baddy57/Eurocrack-Synth/PCB/Project_BIG MODULE_2021-10-10_22-04-19/6692469059dd4fbcb03a7d1d1fd7e01f.png

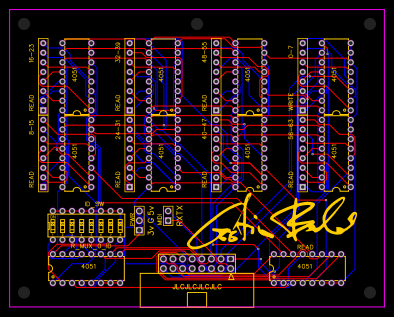
PCB/Project_BIG MODULE_2021-10-10_22-04-19/6692469059dd4fbcb03a7d1d1fd7e01f.png
