baddy57/Eurocrack-Synth/PCB/Project_BIG MODULE_2021-10-10_22-04-19/cb9d58b61e2843a09f57b589a00e0fff.png

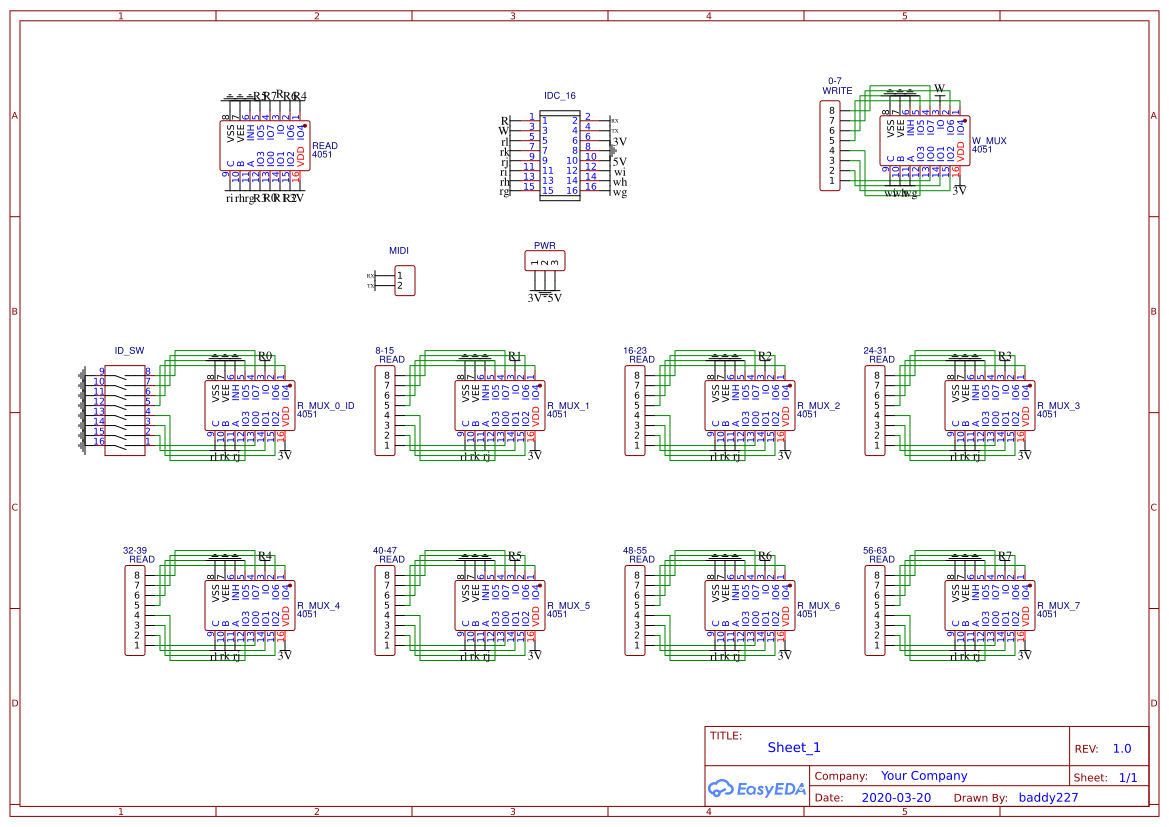
PCB/Project_BIG MODULE_2021-10-10_22-04-19/cb9d58b61e2843a09f57b589a00e0fff.png
