baddy57/Eurocrack-Synth/PCB/Project_MOBO_V3_2021-10-10_21-53-30/35c06b1600684f018b25b84a989f6b6b.png

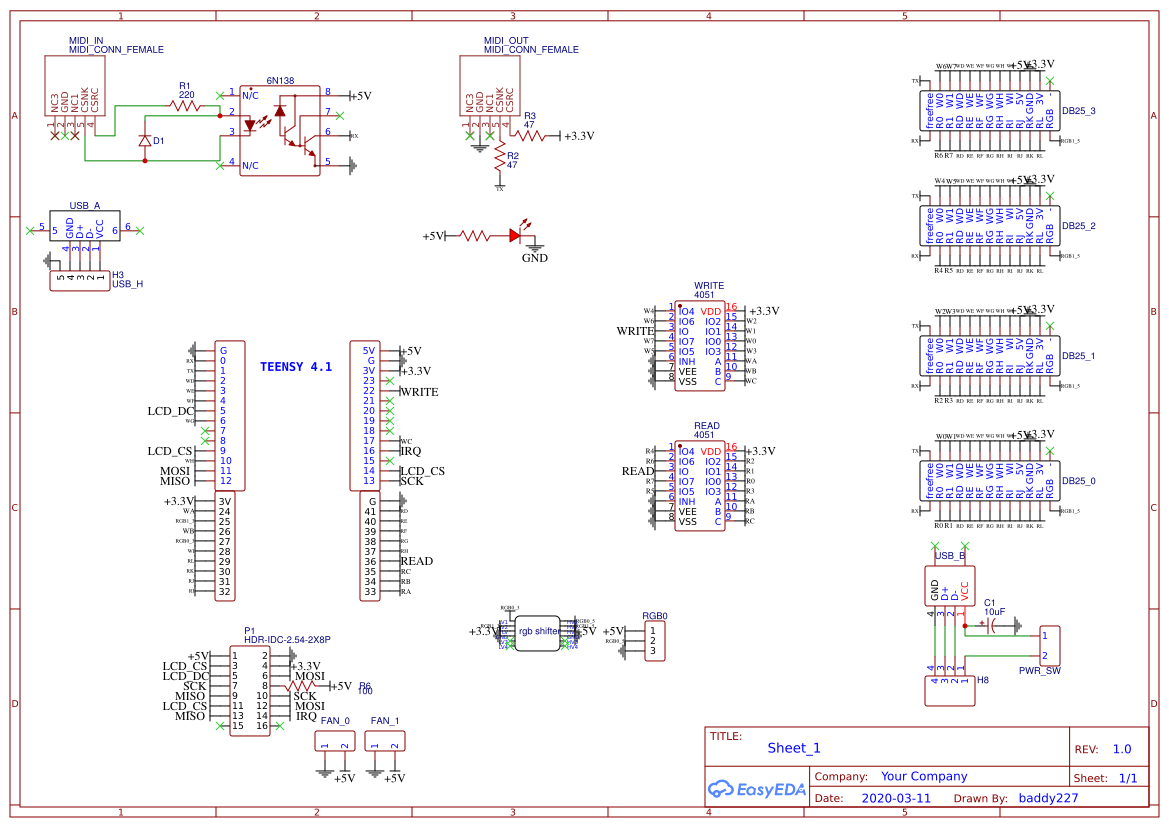
PCB/Project_MOBO_V3_2021-10-10_21-53-30/35c06b1600684f018b25b84a989f6b6b.png
