baddy57/Eurocrack-Synth/PCB/Project_MOBO_V3_2021-10-10_21-53-30/dce181980c11422688b88957aae91851.png

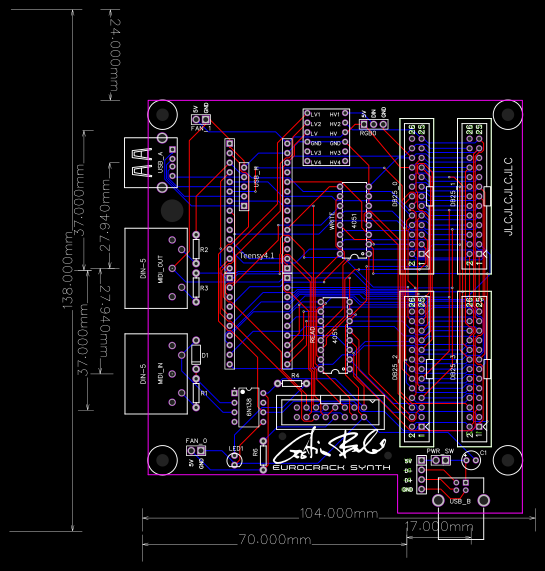
PCB/Project_MOBO_V3_2021-10-10_21-53-30/dce181980c11422688b88957aae91851.png
