baddy57/Eurocrack-Synth/PCB/Project_rack16_A_2021-10-10_22-05-13/7f478ecbd85349aaa525f855d9b86b6f.png

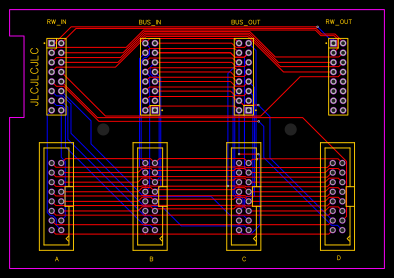
PCB/Project_rack16_A_2021-10-10_22-05-13/7f478ecbd85349aaa525f855d9b86b6f.png
