baddy57/Eurocrack-Synth/PCB/Project_rack16_A_2021-10-10_22-05-13/67f26889370e4767ae0cf2448eb2ead9.png

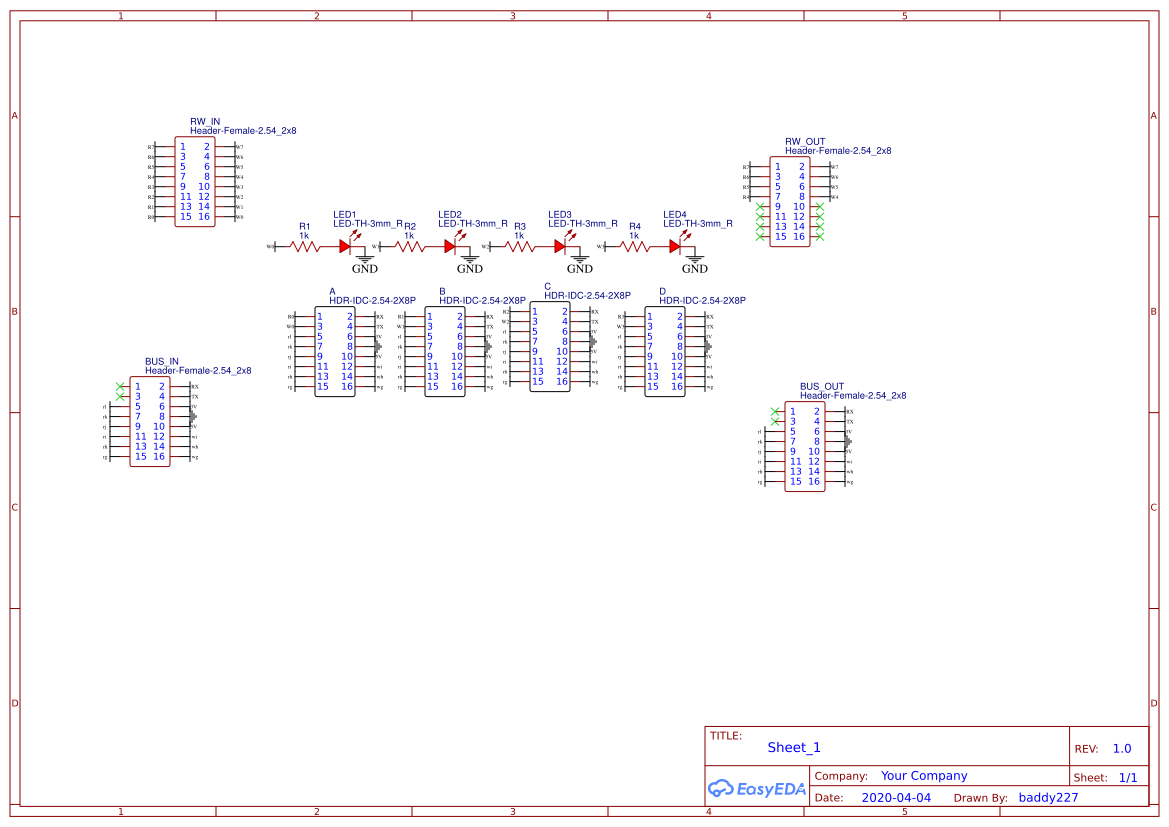
PCB/Project_rack16_A_2021-10-10_22-05-13/67f26889370e4767ae0cf2448eb2ead9.png
