baddy57/Eurocrack-Synth/PCB/Project_rack16_A_2021-10-10_22-05-13/b495c26256024feaad5c0fe8e8caf77f.png

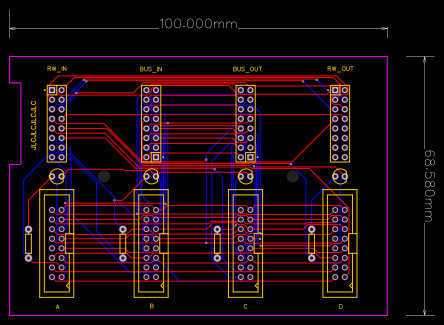
PCB/Project_rack16_A_2021-10-10_22-05-13/b495c26256024feaad5c0fe8e8caf77f.png
