baddy57/Eurocrack-Synth/PCB/Project_rack16_B_2021-10-10_22-06-08/38ca80ff898442d894452e9962c680d8.png

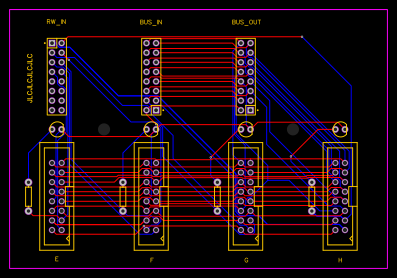
PCB/Project_rack16_B_2021-10-10_22-06-08/38ca80ff898442d894452e9962c680d8.png
