baddy57/Eurocrack-Synth/PCB/Project_RACK16_V3_2021-10-10_21-55-52/4ebbea798132460089381a975b632577.png

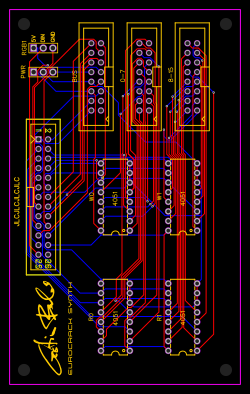
PCB/Project_RACK16_V3_2021-10-10_21-55-52/4ebbea798132460089381a975b632577.png
