baddy57/Eurocrack-Synth/PCB/Project_RACK16_V3_2021-10-10_21-55-52/cc3ec4de50fb47bfaea3014c30f05088.png

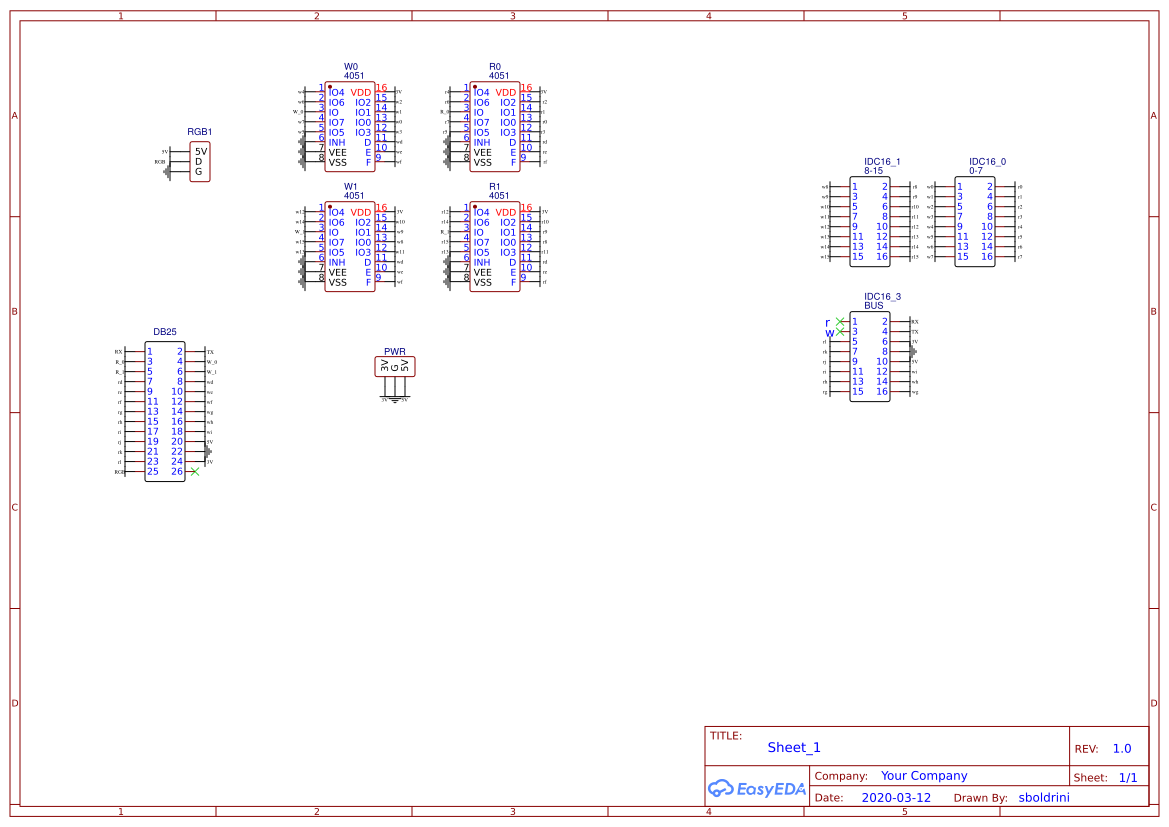
PCB/Project_RACK16_V3_2021-10-10_21-55-52/cc3ec4de50fb47bfaea3014c30f05088.png
