baddy57/Eurocrack-Synth/PCB/Project_SMALL MODULE_2021-10-10_22-03-08/b1a0076e745e476ea71988d6097ee347.png

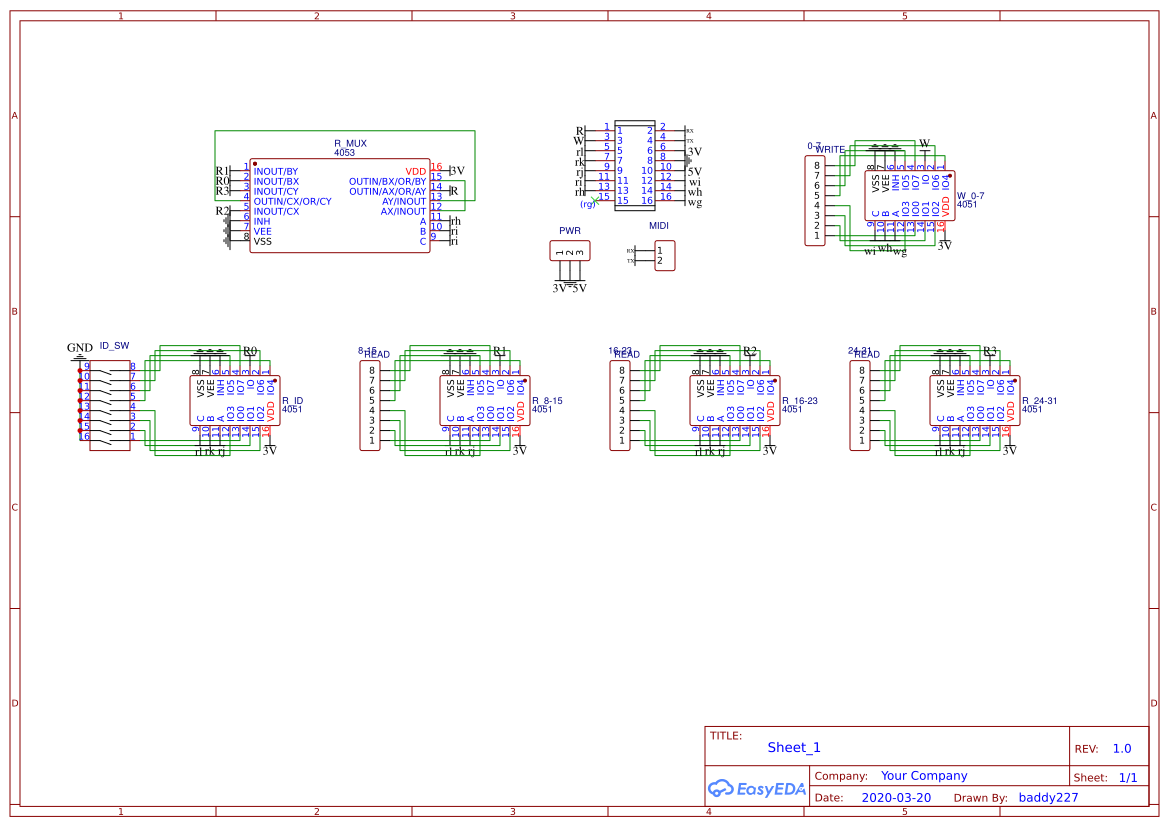
PCB/Project_SMALL MODULE_2021-10-10_22-03-08/b1a0076e745e476ea71988d6097ee347.png
