baddy57/Eurocrack-Synth/3D PARTS/MASTER BOX/ic_mic_48px-512.webp

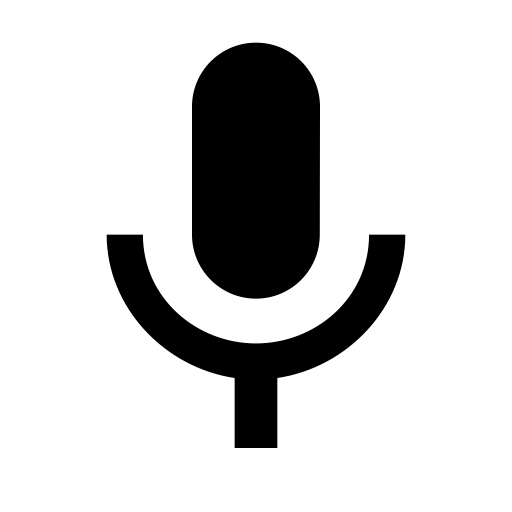
3D PARTS/MASTER BOX/ic_mic_48px-512.webp
