baddy57/Eurocrack-Synth/3D PARTS/MASTER BOX/PCB.png

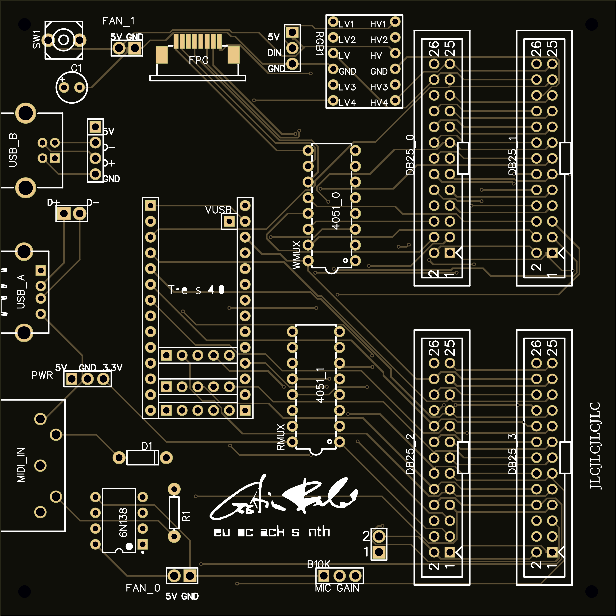
3D PARTS/MASTER BOX/PCB.png
