baddy57/Eurocrack-Synth/3D PARTS/MODULES/BIG PCB.jpg

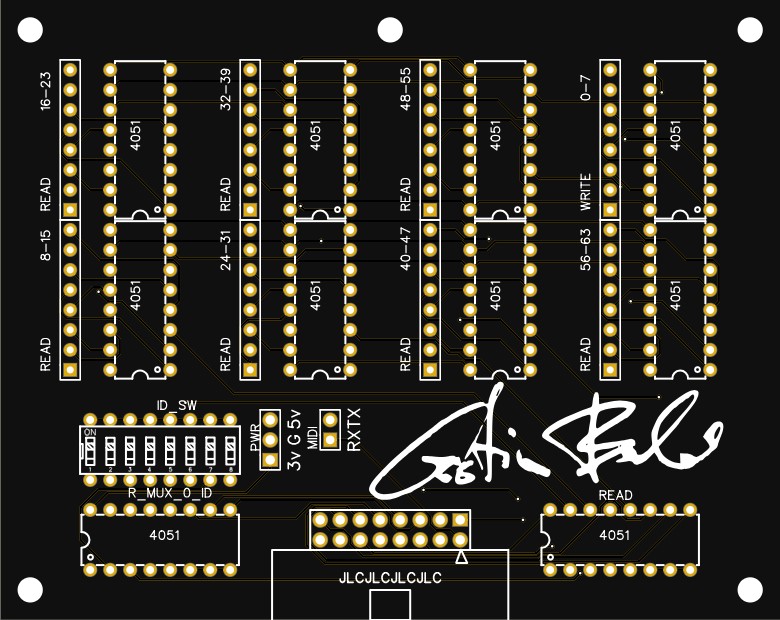
3D PARTS/MODULES/BIG PCB.jpg
