baddy57/Eurocrack-Synth/3D PARTS/MODULES/MODULE PCB TYPE A.png

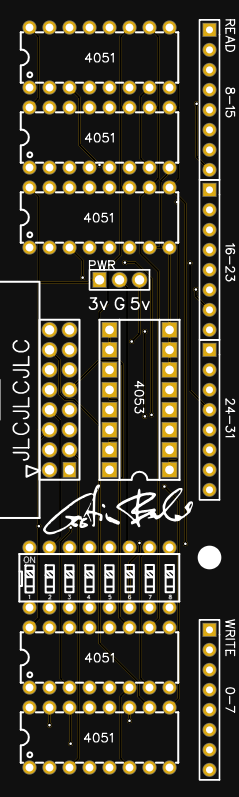
3D PARTS/MODULES/MODULE PCB TYPE A.png
