baddy57/Eurocrack-Synth/3D PARTS/RACK16/trash/Parametric_Eurorack_Rail2/images/62bd9fd48c2334298f00ef797886a475_preview_featured.jpg

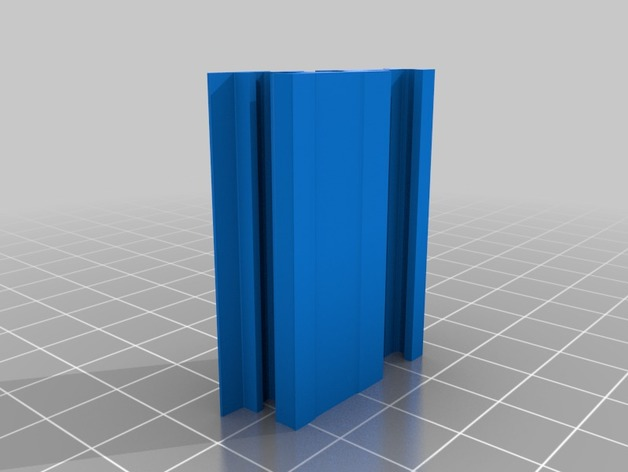
3D PARTS/RACK16/trash/Parametric_Eurorack_Rail2/images/62bd9fd48c2334298f00ef797886a475_preview_featured.jpg
