baddy57/Eurocrack-Synth/3D PARTS/RACK16/trash/Parametric_Eurorack_Rail/images/9bb14bf8cfc0c23107f52e55db40d1ac_preview_featured.JPG

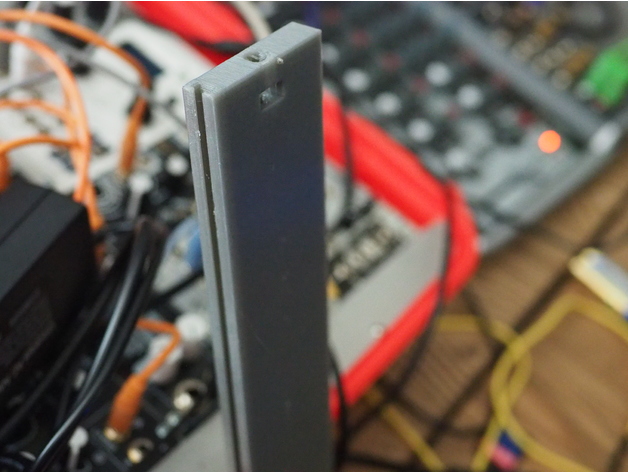
3D PARTS/RACK16/trash/Parametric_Eurorack_Rail/images/9bb14bf8cfc0c23107f52e55db40d1ac_preview_featured.JPG
