baddy57/Eurocrack-Synth/3D PARTS/RACK16/trash/Parametric_Eurorack_Rail/images/365d9e6f2081d008faea3ab9caef1937_preview_featured.jpg

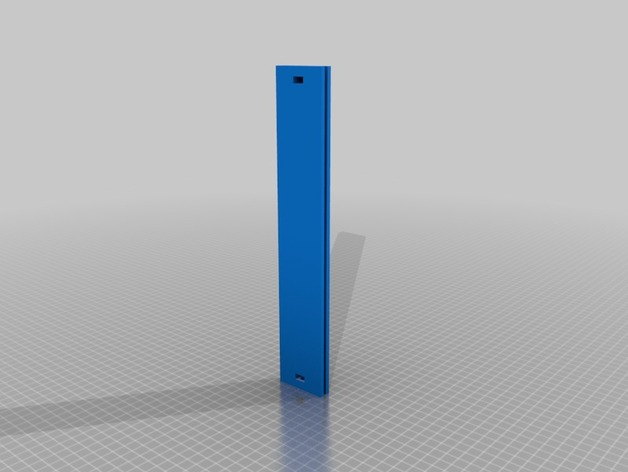
3D PARTS/RACK16/trash/Parametric_Eurorack_Rail/images/365d9e6f2081d008faea3ab9caef1937_preview_featured.jpg
