baddy57/Eurocrack-Synth/3D PARTS/RACK16/trash/Parametric_Eurorack_Rail/images/882311587377e1cdbaf4c9a8b8c7068b_preview_featured.jpg

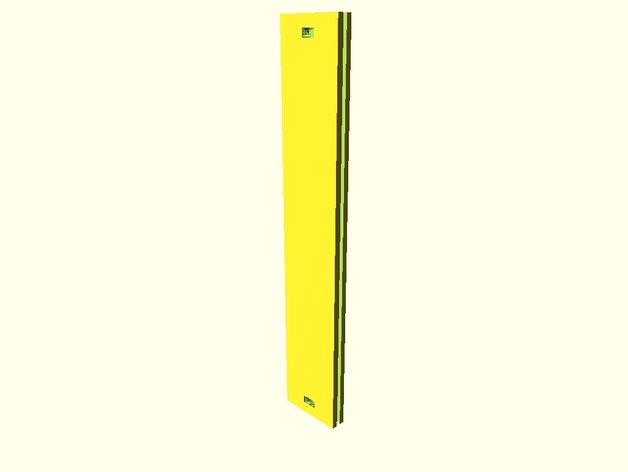
3D PARTS/RACK16/trash/Parametric_Eurorack_Rail/images/882311587377e1cdbaf4c9a8b8c7068b_preview_featured.jpg
