baddy57/Eurocrack-Synth/3D PARTS/RACK16/RGB_EPOXY_v5_negativo.stl

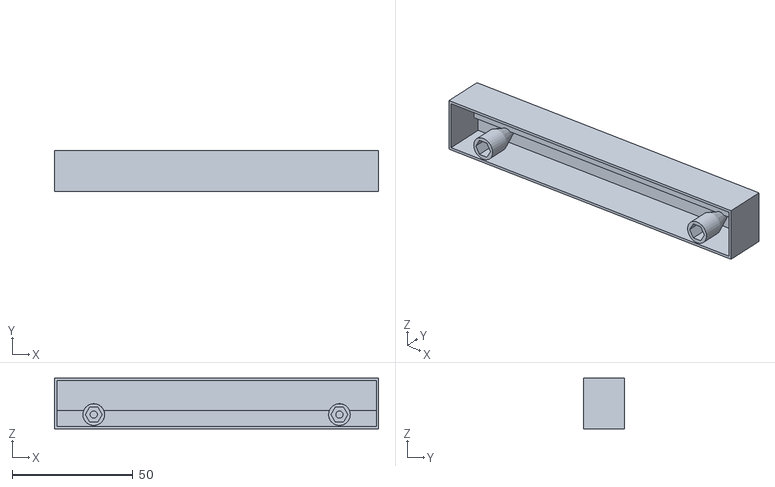
[picture p39: CAD file, 2021-10-12]
3D PARTS/RACK16/RGB_EPOXY_v5_negativo.stl
134.0 x 17.0 x 21.0
