baddy57/Eurocrack-Synth/3D PARTS/MASTER BOX/MASTER_AUDIO_IO_PANEL_V2.stl

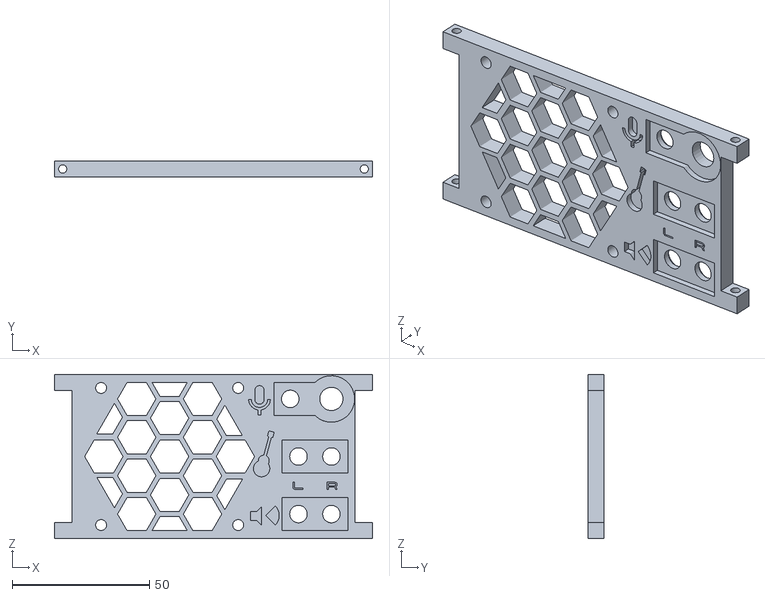
[picture p40: CAD file, 2021-10-12]
3D PARTS/MASTER BOX/MASTER_AUDIO_IO_PANEL_V2.stl
116.0 x 6.00 x 60.0
