baddy57/Eurocrack-Synth/3D PARTS/MODULES/20HP_MIXER8.FCStd

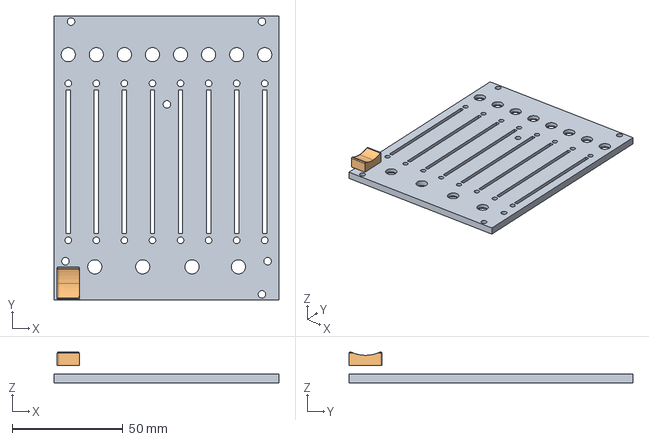
[picture p41: CAD file, 2021-10-12]
3D PARTS/MODULES/20HP_MIXER8.FCStd
101.6 x 128.5 x 14.0 mm
