baddy57/Eurocrack-Synth/3D PARTS/RACK16/trash/strip.FCStd

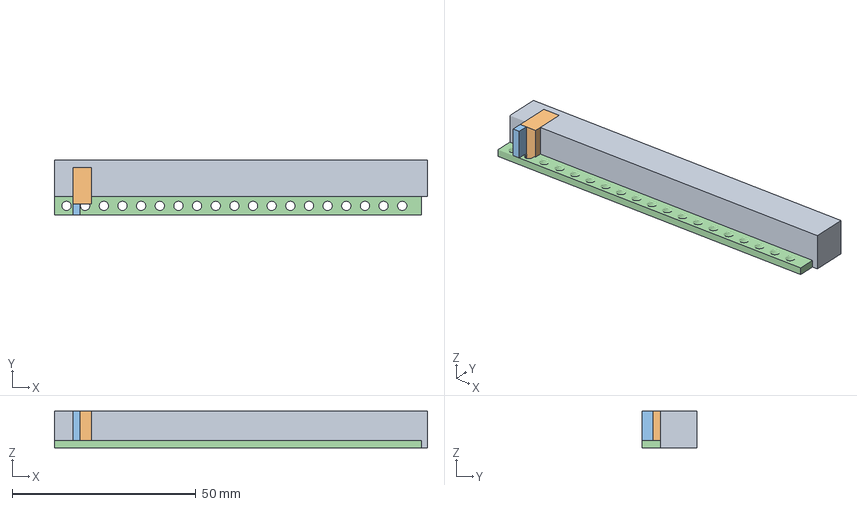
[picture p43: CAD file, 2021-10-12]
3D PARTS/RACK16/trash/strip.FCStd
101.6 x 15.0 x 10.0 mm
eurorack_threaded_strip
