baddy57/Eurocrack-Synth/3D PARTS/MASTER BOX/MASTER_MIDI_PANEL.stl

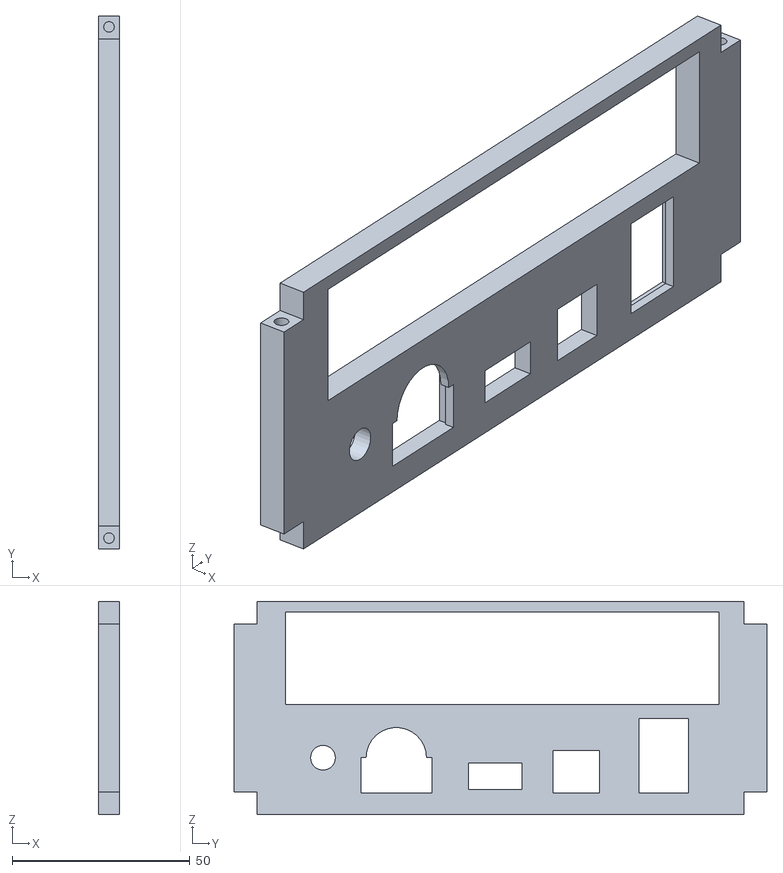
[picture p44: CAD file, 2021-10-12]
3D PARTS/MASTER BOX/MASTER_MIDI_PANEL.stl
6.00 x 150.0 x 60.0
