baddy57/Eurocrack-Synth/3D PARTS/MODULES/3HP_AUDIOOUT.FCStd

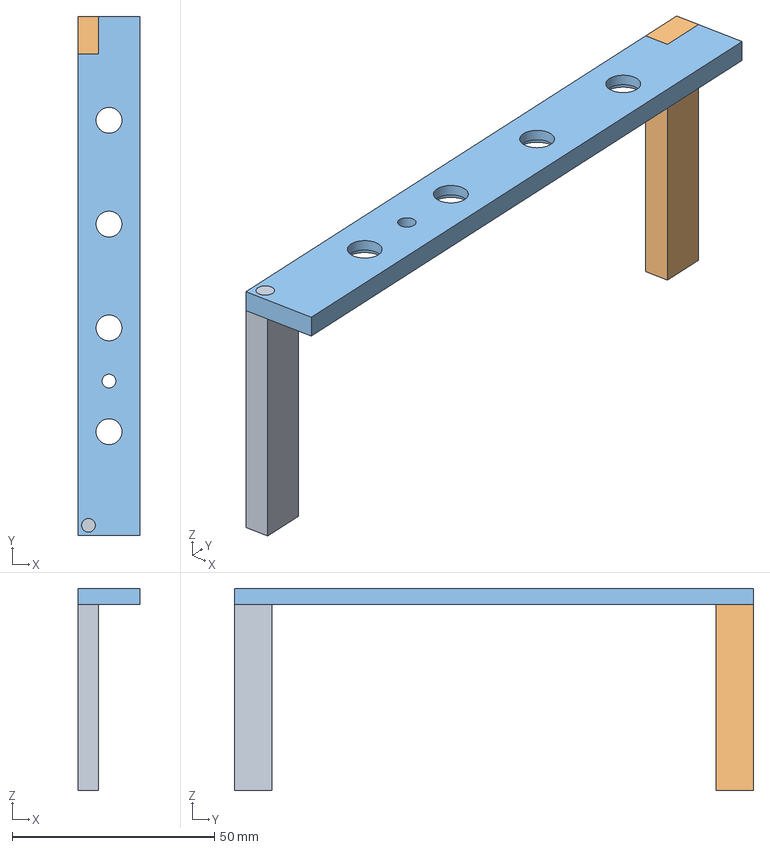
[picture p45: CAD file, 2021-10-12]
3D PARTS/MODULES/3HP_AUDIOOUT.FCStd
15.2 x 128.5 x 50.0 mm
