baddy57/Eurocrack-Synth/3D PARTS/RACK16/RGB_EPOXY_p2.stl

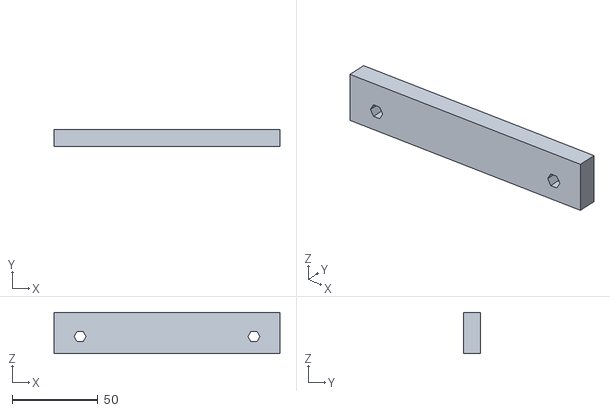
[picture p46: CAD file, 2021-10-12]
3D PARTS/RACK16/RGB_EPOXY_p2.stl
132.1 x 10.0 x 24.0
