baddy57/Eurocrack-Synth/3D PARTS/RACK16/trash/rail 12hp.FCStd

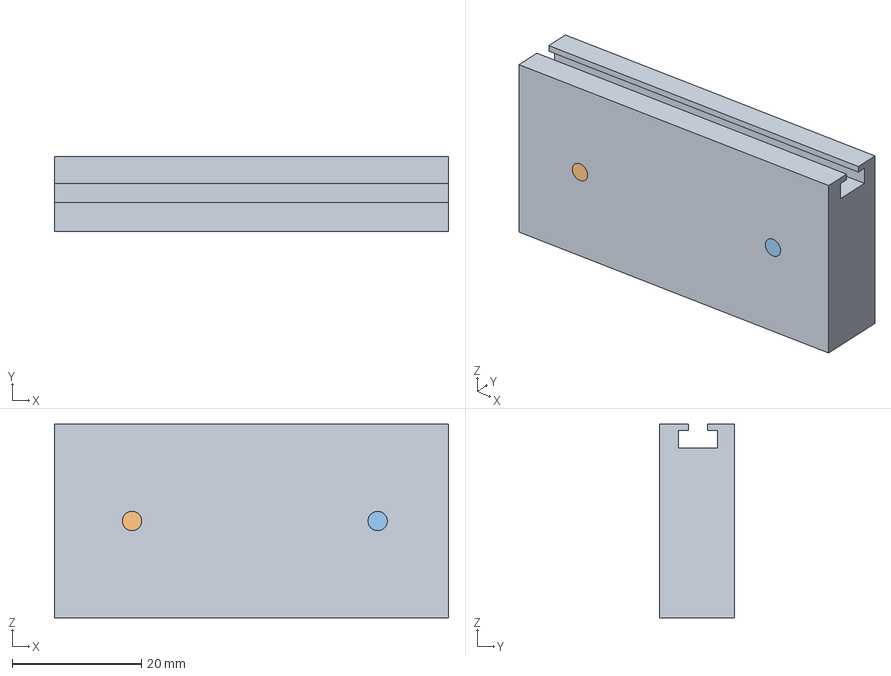
[picture p47: CAD file, 2021-10-12]
3D PARTS/RACK16/trash/rail 12hp.FCStd
61.0 x 11.7 x 30.0 mm
