baddy57/Eurocrack-Synth/3D PARTS/MASTER BOX/MASTER BOX_v3.FCStd

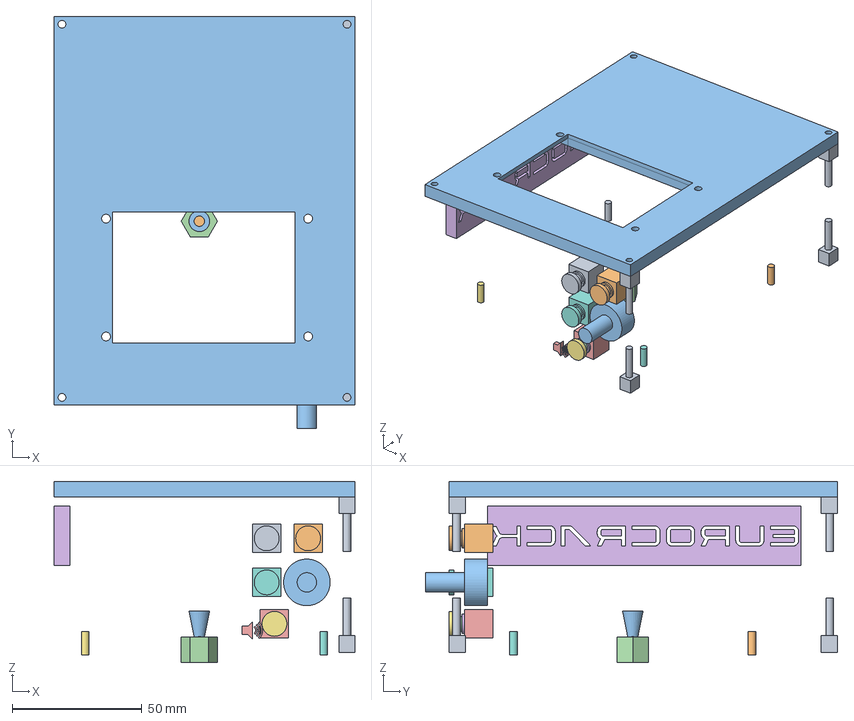
[picture p48: CAD file, 2021-10-12]
3D PARTS/MASTER BOX/MASTER BOX_v3.FCStd
116.0 x 159.0 x 70.0 mm
wall joints
jack 3.5 mono004
jack 3.5 mono003
jack 3.5 mono005
jack mono002
jack mono003
jack mono004
mic gain
speaker icon
LOGO
