baddy57/Eurocrack-Synth/3D PARTS/MODULES/socket spacing.stl

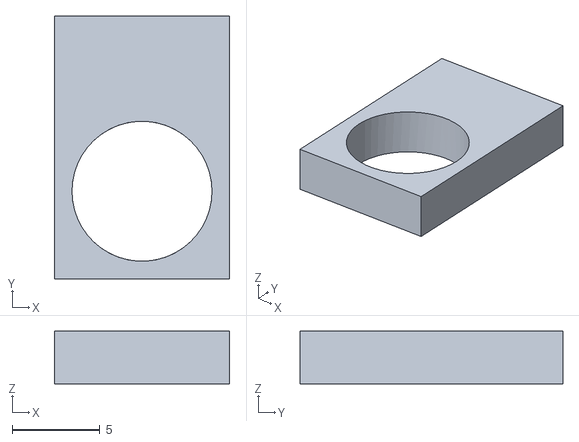
[picture p49: CAD file, 2021-10-12]
3D PARTS/MODULES/socket spacing.stl
10.0 x 15.0 x 3.00
