baddy57/Eurocrack-Synth/3D PARTS/RACK16/26_HP.FCStd

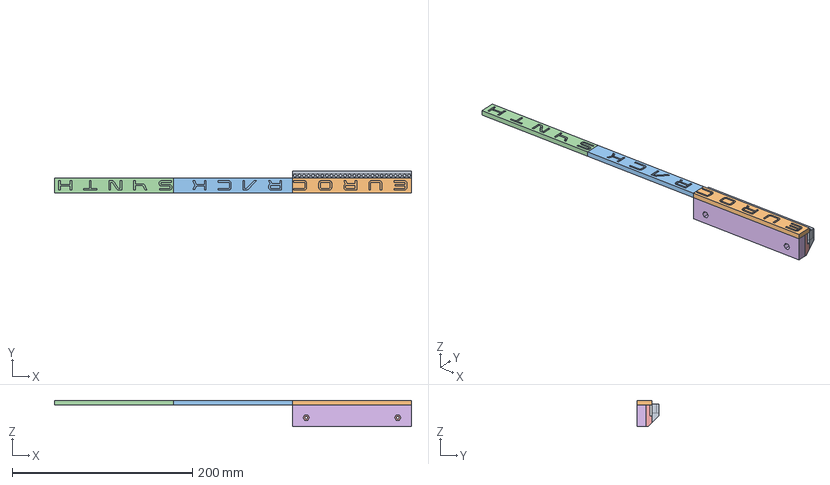
[picture p50: CAD file, 2021-10-12]
3D PARTS/RACK16/26_HP.FCStd
396.2 x 24.0 x 29.0 mm
26HP_BRACKET
EUROC
RACK
SYNTH
p1
p2
