baddy57/Eurocrack-Synth/3D PARTS/RACK16/trash/SHIELD.stl

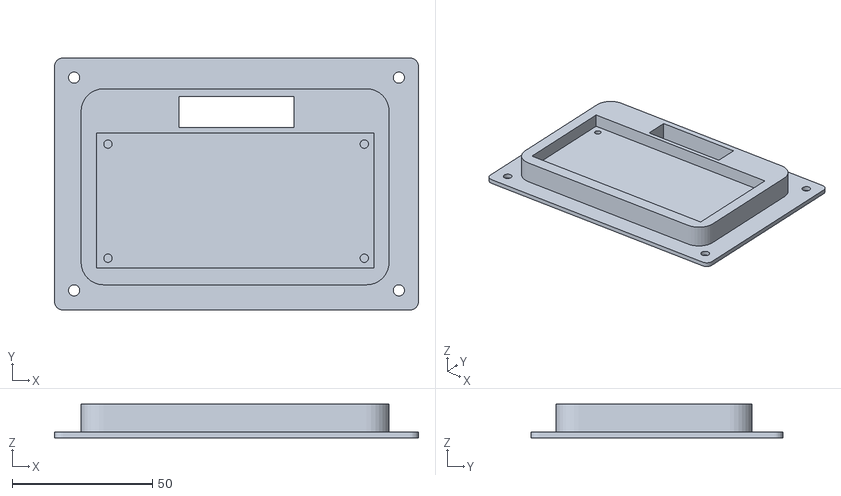
[picture p51: CAD file, 2021-10-12]
3D PARTS/RACK16/trash/SHIELD.stl
130.0 x 90.0 x 12.0
