baddy57/Eurocrack-Synth/3D PARTS/MASTER BOX/MASTER_BOTTOM.stl

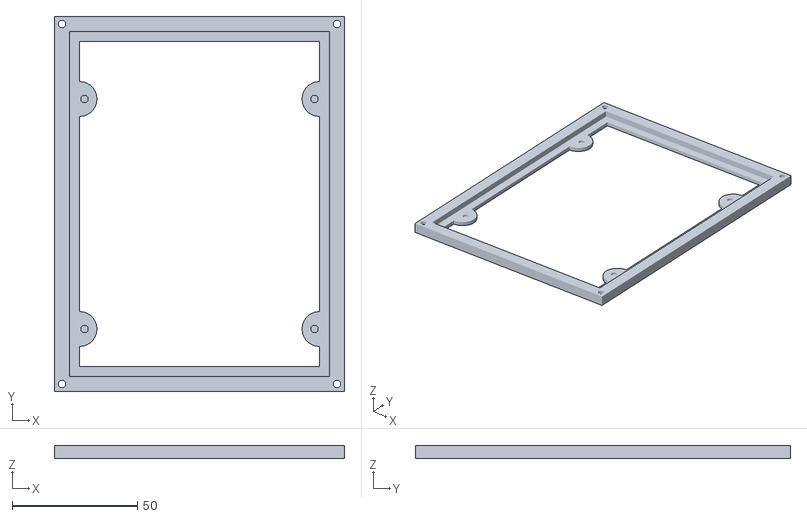
[picture p52: CAD file, 2021-10-12]
3D PARTS/MASTER BOX/MASTER_BOTTOM.stl
116.0 x 150.0 x 5.00
