baddy57/Eurocrack-Synth/3D PARTS/MODULES/6HP_HOLDER_P1.stl

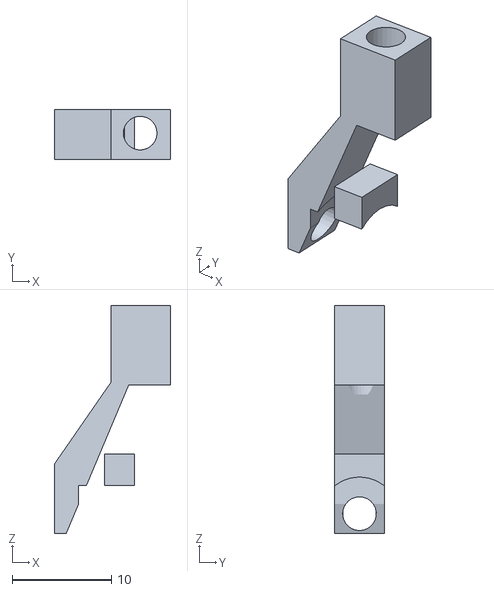
[picture p53: CAD file, 2021-10-12]
3D PARTS/MODULES/6HP_HOLDER_P1.stl
11.7 x 5.00 x 23.0
