baddy57/Eurocrack-Synth/3D PARTS/RACK16/RGB_EPOXY_p2_NEGATIVO.stl

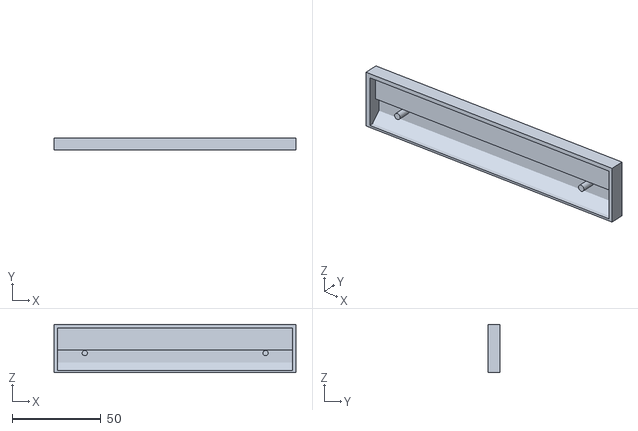
[picture p54: CAD file, 2021-10-12]
3D PARTS/RACK16/RGB_EPOXY_p2_NEGATIVO.stl
136.0 x 7.00 x 27.0
