baddy57/Eurocrack-Synth/3D PARTS/MASTER BOX/MASTER_DB25_PANEL.stl

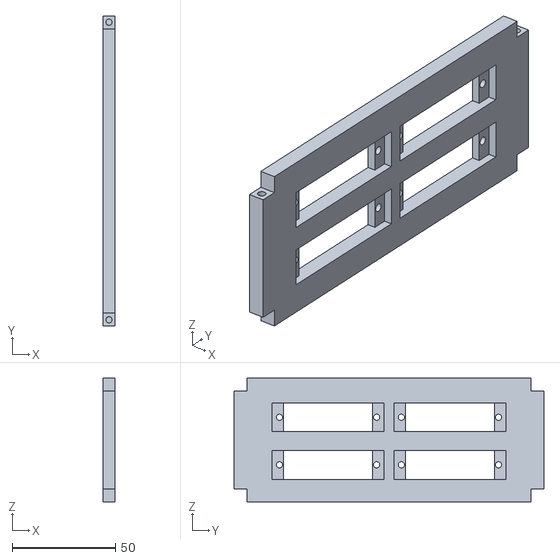
[picture p55: CAD file, 2021-10-12]
3D PARTS/MASTER BOX/MASTER_DB25_PANEL.stl
6.00 x 150.0 x 60.0
