baddy57/Eurocrack-Synth/3D PARTS/MODULES/3HP_VCAx2.FCStd

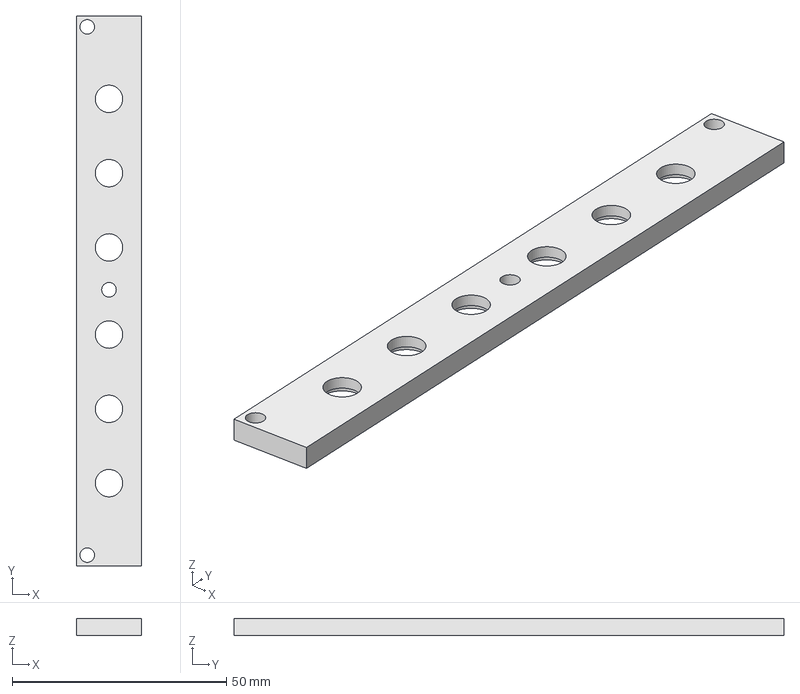
[picture p56: CAD file, 2021-10-12]
3D PARTS/MODULES/3HP_VCAx2.FCStd
15.2 x 128.5 x 4.00 mm
