baddy57/Eurocrack-Synth/3D PARTS/RACK16/RGB_EPOXY_p1.stl

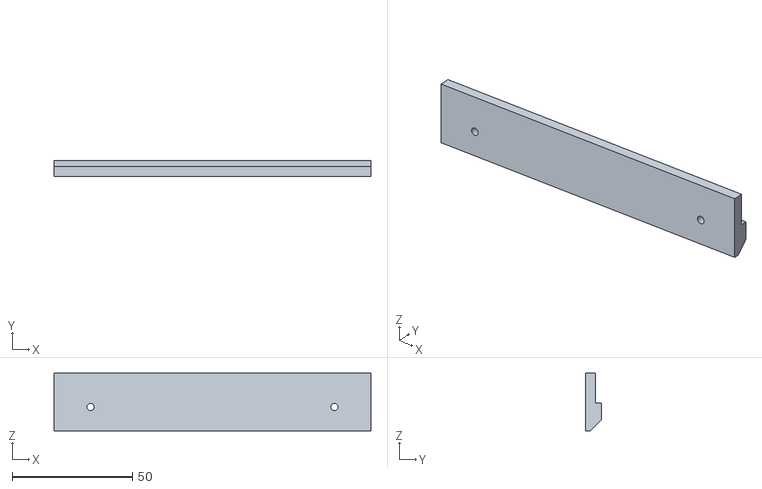
[picture p57: CAD file, 2021-10-12]
3D PARTS/RACK16/RGB_EPOXY_p1.stl
132.1 x 6.49 x 24.0
