baddy57/Eurocrack-Synth/3D PARTS/RACK16/trash/rail buona senza strip.FCStd

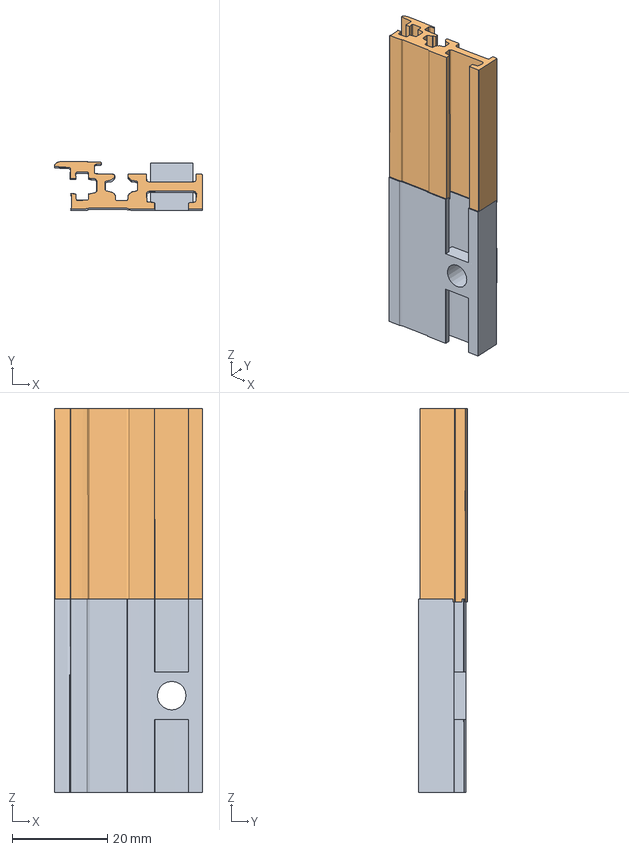
[picture p58: CAD file, 2021-10-12]
3D PARTS/RACK16/trash/rail buona senza strip.FCStd
31.2 x 10.3 x 80.7 mm
Eurorack_Rail_8HP_with_holes
Eurorack_Rail_8HP_Gie_Tec
