baddy57/Eurocrack-Synth/3D PARTS/MODULES/pcb.FCStd

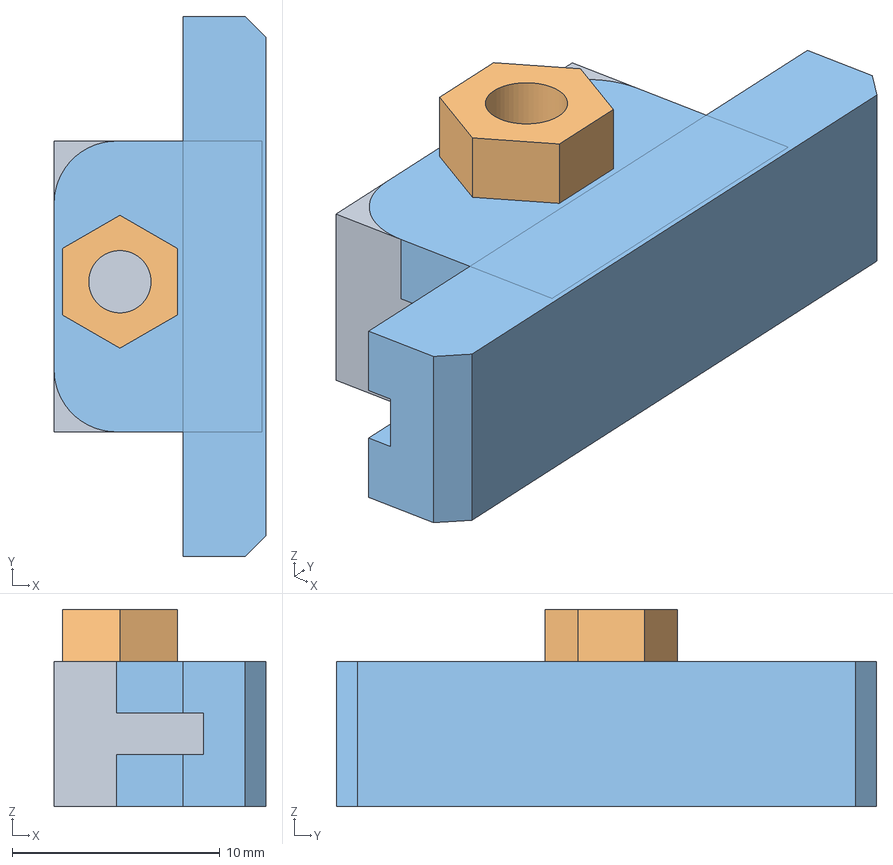
[picture p59: CAD file, 2021-10-12]
3D PARTS/MODULES/pcb.FCStd
10.2 x 26.0 x 9.50 mm
hex_nut
pcb_mnt
