baddy57/Eurocrack-Synth/3D PARTS/RACK16/trash/border.FCStd

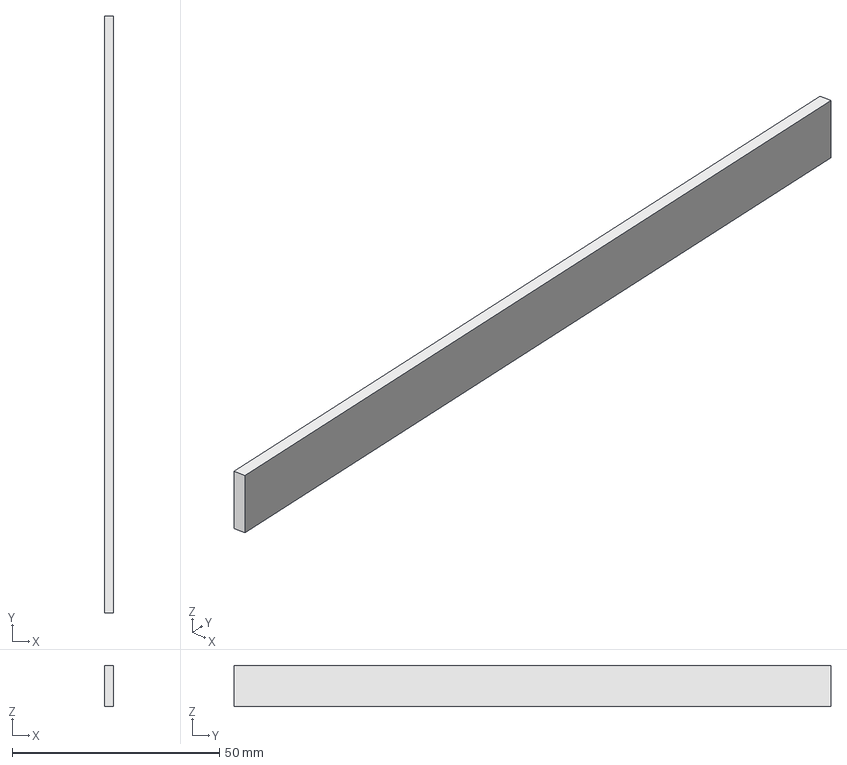
[picture p61: CAD file, 2021-10-12]
3D PARTS/RACK16/trash/border.FCStd
2.10 x 144.0 x 10.0 mm
