baddy57/Eurocrack-Synth/3D PARTS/MODULES/VCF.stl

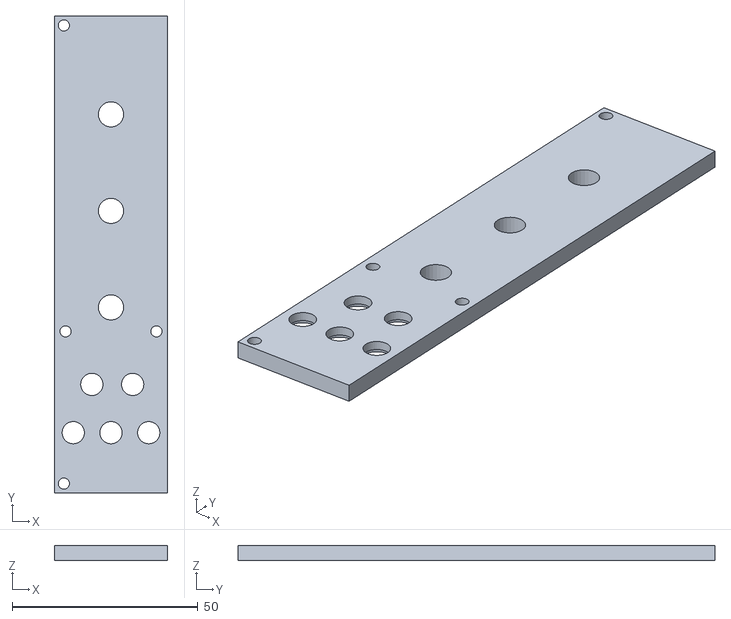
[picture p62: CAD file, 2021-10-12]
3D PARTS/MODULES/VCF.stl
30.5 x 128.5 x 4.00
