baddy57/Eurocrack-Synth/3D PARTS/RACK16/RACK16.FCStd

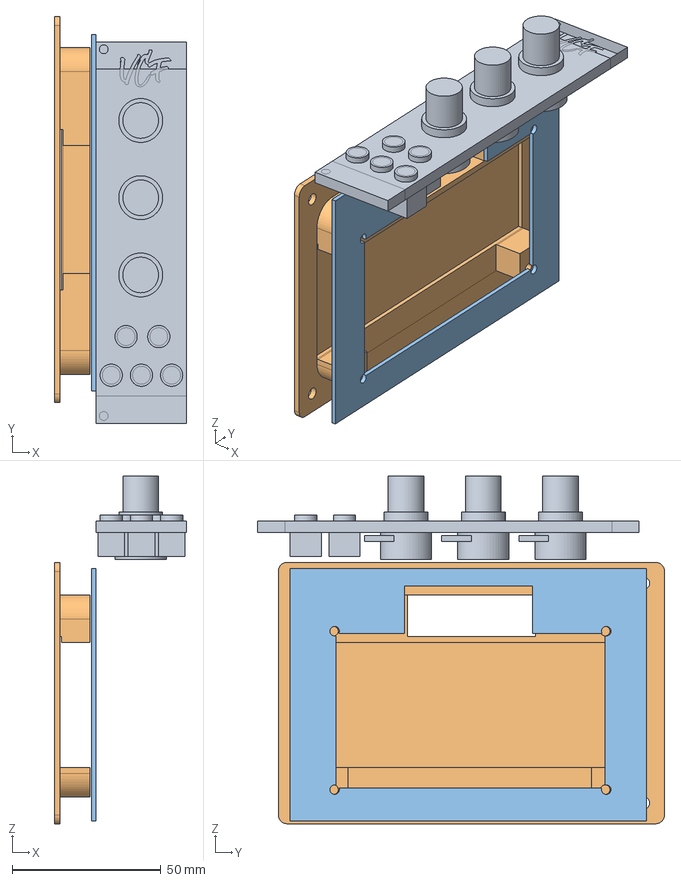
[picture p63: CAD file, 2021-10-12]
3D PARTS/RACK16/RACK16.FCStd
44.6 x 137.0 x 117.0 mm
VCF
shield003
shield int.
