baddy57/Eurocrack-Synth/3D PARTS/RACK16/trash/SHIELD_v2.stl

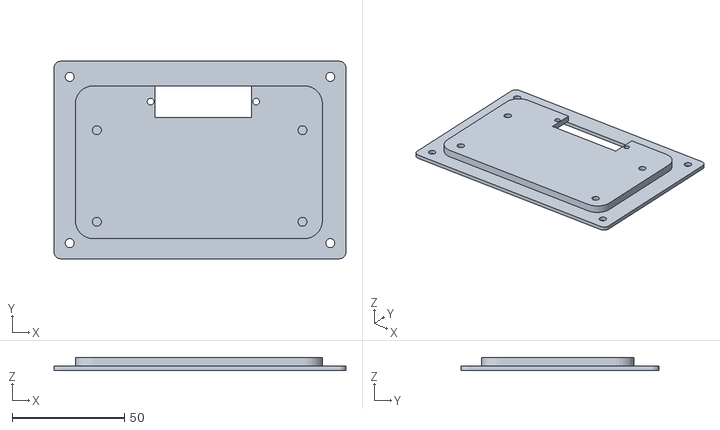
[picture p64: CAD file, 2021-10-12]
3D PARTS/RACK16/trash/SHIELD_v2.stl
130.0 x 88.0 x 6.00
