baddy57/Eurocrack-Synth/3D PARTS/MODULES/3HP_HOLDER.stl

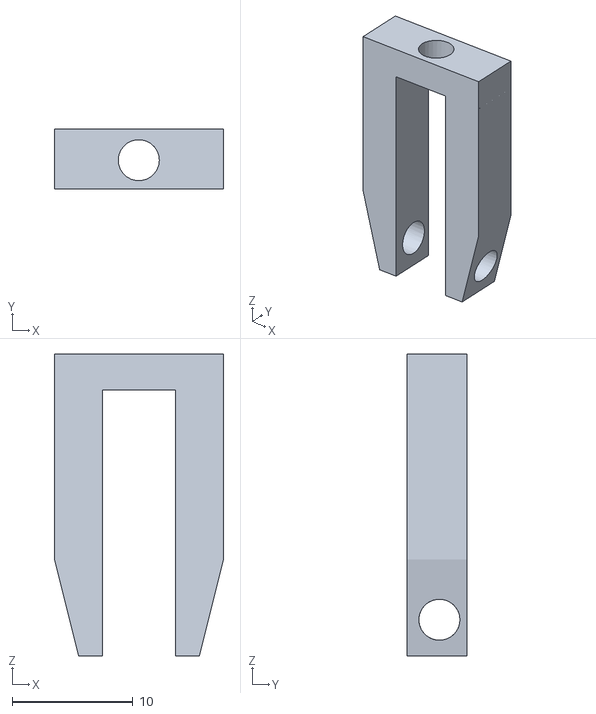
[picture p65: CAD file, 2021-10-12]
3D PARTS/MODULES/3HP_HOLDER.stl
14.0 x 5.00 x 25.0
