baddy57/Eurocrack-Synth/3D PARTS/MODULES/8HP_VCO-LFO.FCStd

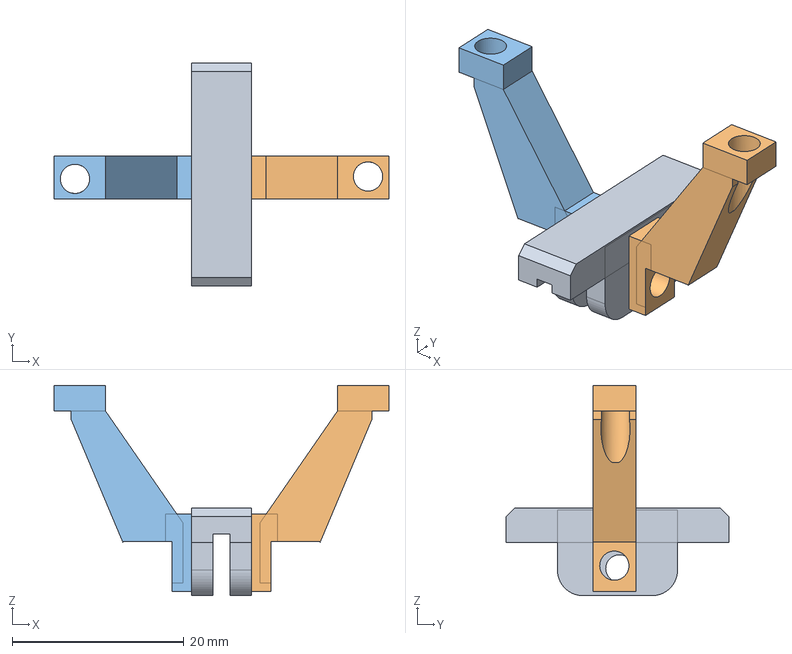
[picture p67: CAD file, 2021-10-12]
3D PARTS/MODULES/8HP_VCO-LFO.FCStd
39.0 x 26.0 x 24.5 mm
pcb_mnt
mnt L
mnt R
