baddy57/Eurocrack-Synth/3D PARTS/MODULES/6HP_VCA_x5.FCStd

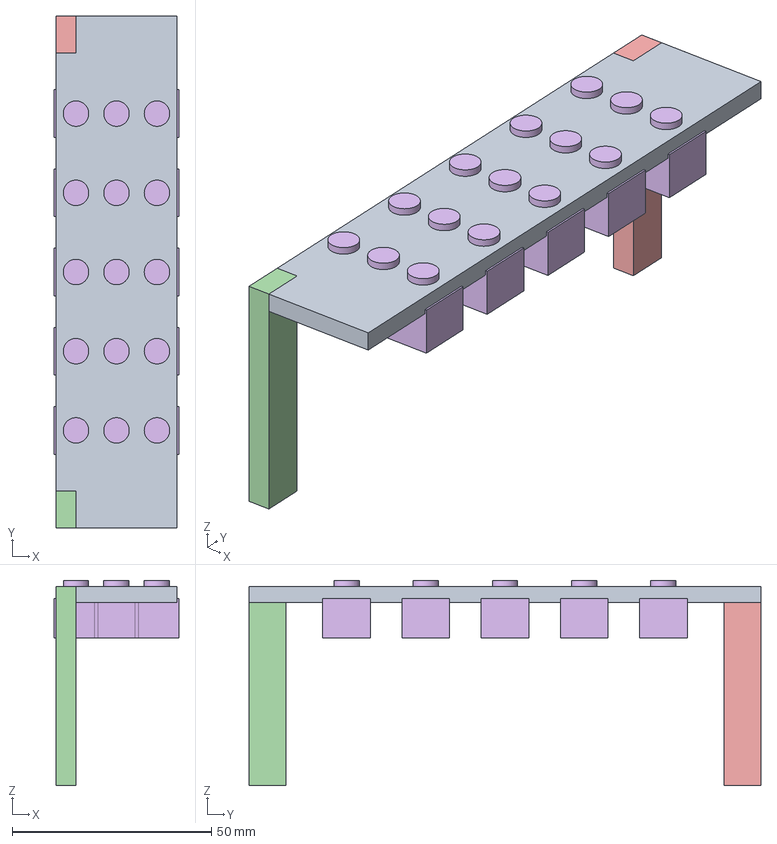
[picture p68: CAD file, 2021-10-12]
3D PARTS/MODULES/6HP_VCA_x5.FCStd
31.3 x 128.5 x 51.5 mm
M3 SCREW
M3 SCREW001
