baddy57/Eurocrack-Synth/3D PARTS/MODULES/_TEMPLATE.FCStd

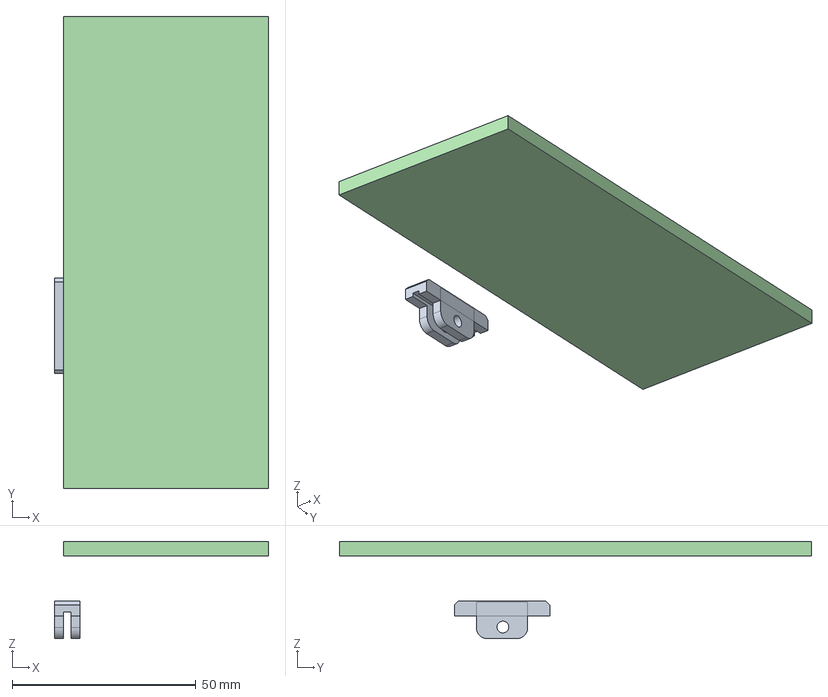
[picture p69: CAD file, 2021-10-12]
3D PARTS/MODULES/_TEMPLATE.FCStd
58.4 x 128.5 x 26.5 mm
pcb_mnt
M3 SCREW
M3 SCREW001
PANEL
M3 SCREW002
M3 SCREW003
