baddy57/Eurocrack-Synth/3D PARTS/RACK16/RACK16_SHIELD_V3.FCStd

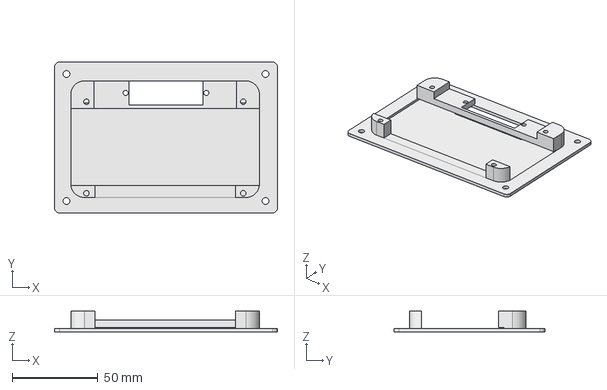
[picture p70: CAD file, 2021-10-12]
3D PARTS/RACK16/RACK16_SHIELD_V3.FCStd
130.0 x 88.0 x 12.0 mm
