baddy57/Eurocrack-Synth/3D PARTS/MODULES/4HP_AUDIOIN.FCStd

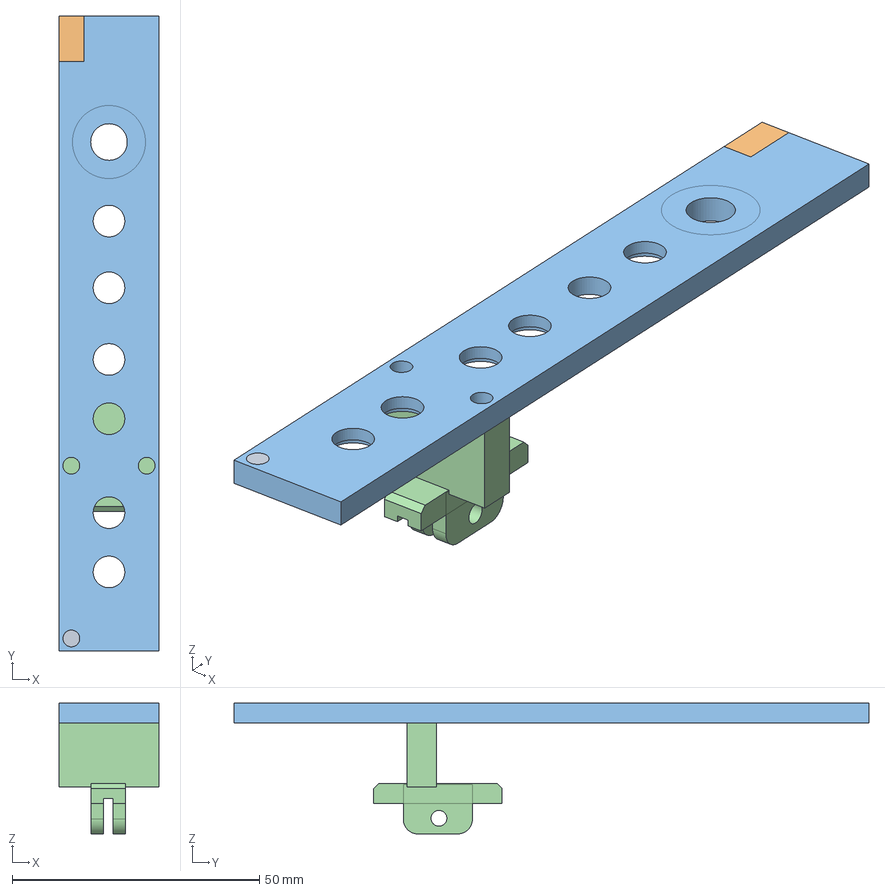
[picture p71: CAD file, 2021-10-12]
3D PARTS/MODULES/4HP_AUDIOIN.FCStd
20.3 x 128.5 x 26.5 mm
