baddy57/Eurocrack-Synth/3D PARTS/MODULES/2HP_AUDIOOUT.FCStd

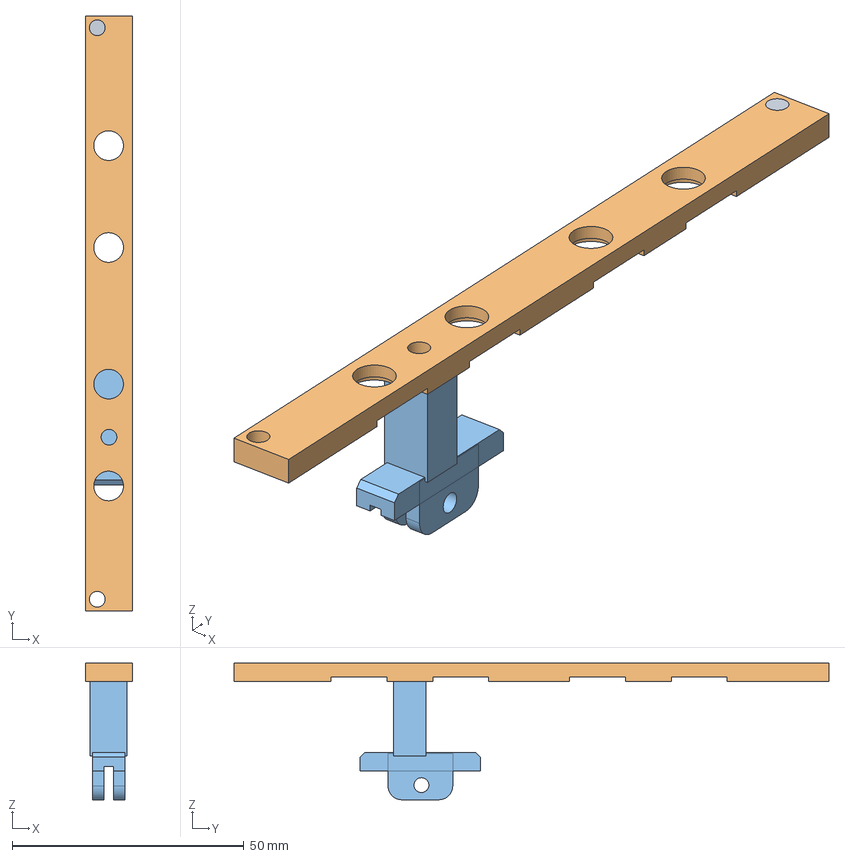
[picture p72: CAD file, 2021-10-12]
3D PARTS/MODULES/2HP_AUDIOOUT.FCStd
10.2 x 128.5 x 29.5 mm
