baddy57/Eurocrack-Synth/3D PARTS/RACK16/LOGO_EUROC.stl

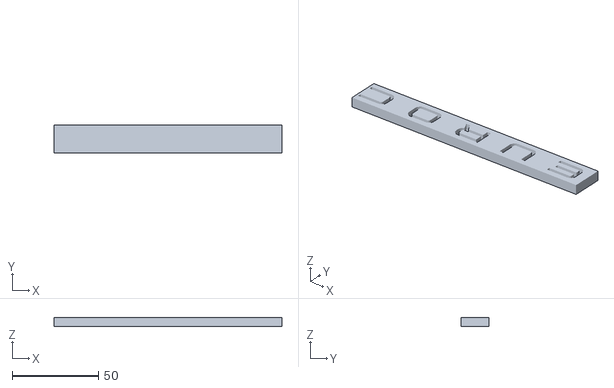
[picture p73: CAD file, 2021-10-12]
3D PARTS/RACK16/LOGO_EUROC.stl
132.1 x 16.5 x 5.00
