baddy57/Eurocrack-Synth/3D PARTS/MODULES/VCA.FCStd

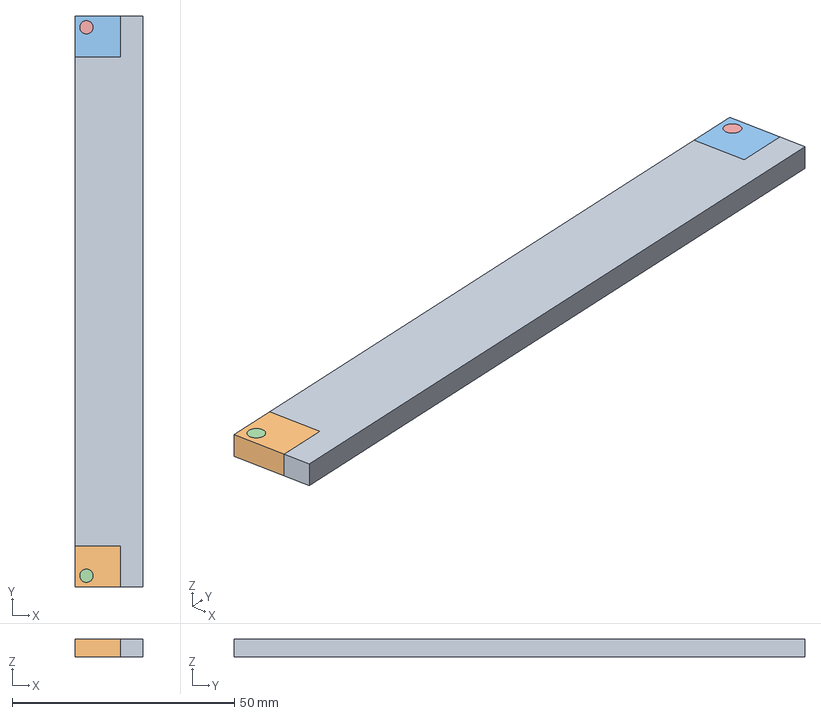
[picture p74: CAD file, 2021-10-12]
3D PARTS/MODULES/VCA.FCStd
15.2 x 128.5 x 4.00 mm
M3 SCREW
M3 SCREW001
