baddy57/Eurocrack-Synth/3D PARTS/MODULES/8HP_HOLDER_P2_V2.stl

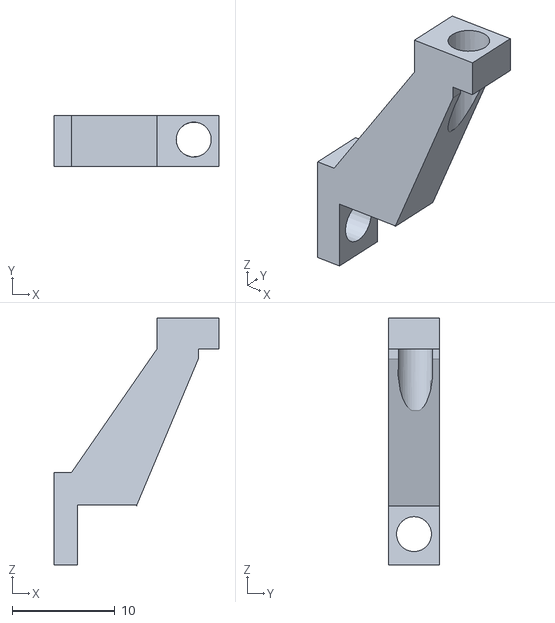
[picture p75: CAD file, 2021-10-12]
3D PARTS/MODULES/8HP_HOLDER_P2_V2.stl
16.0 x 5.00 x 24.0
