baddy57/Eurocrack-Synth/3D PARTS/RACK16/bottom pcb holder.FCStd

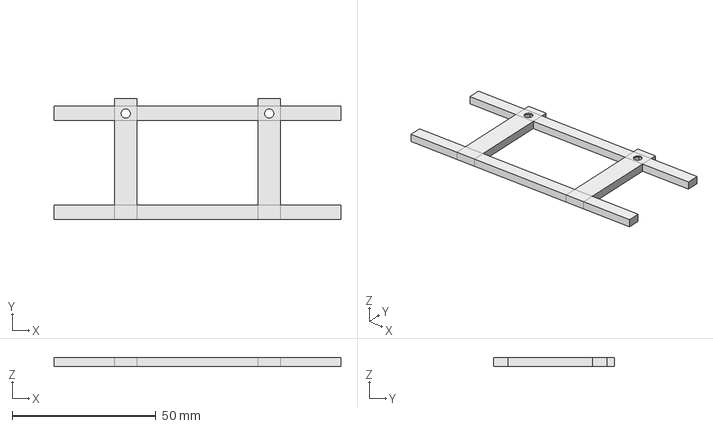
[picture p76: CAD file, 2021-10-12]
3D PARTS/RACK16/bottom pcb holder.FCStd
100.0 x 42.0 x 3.00 mm
