baddy57/Eurocrack-Synth/3D PARTS/MODULES/4HP_PCB.stl

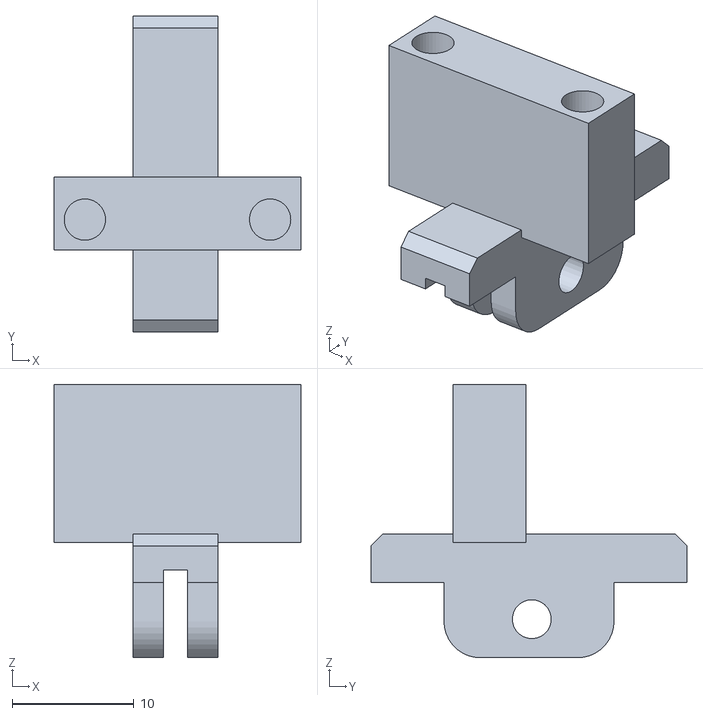
[picture p77: CAD file, 2021-10-12]
3D PARTS/MODULES/4HP_PCB.stl
20.3 x 26.0 x 22.5
