baddy57/Eurocrack-Synth/3D PARTS/MODULES/3HP_MIDI_MONO.FCStd

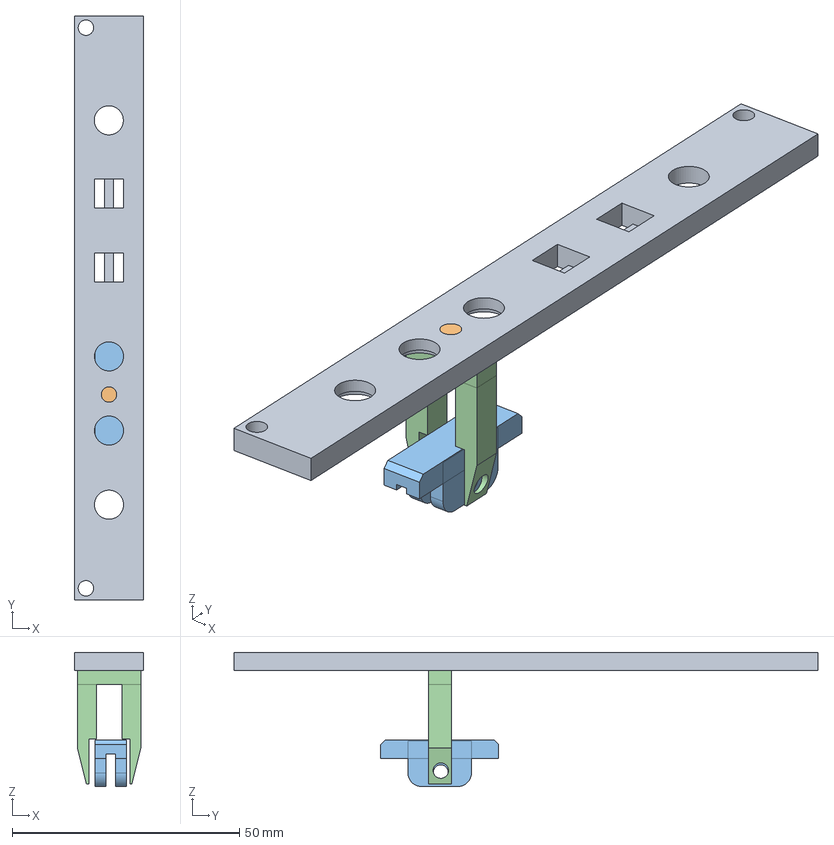
[picture p78: CAD file, 2021-10-12]
3D PARTS/MODULES/3HP_MIDI_MONO.FCStd
15.2 x 128.5 x 29.5 mm
M3 SCREW002
pcb_mnt
