baddy57/Eurocrack-Synth/3D PARTS/MODULES/9HP_DRUMKIT.FCStd

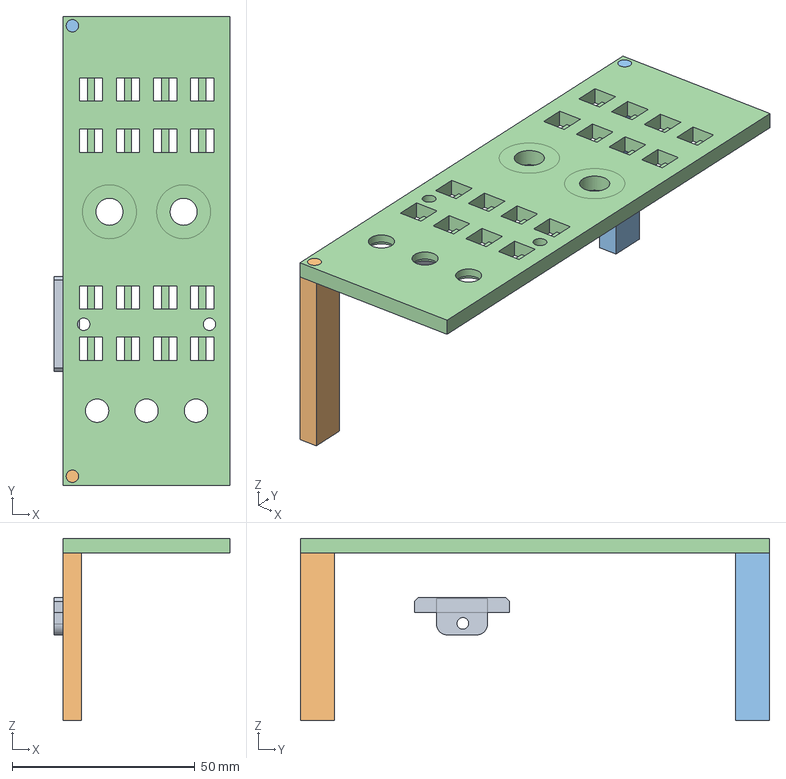
[picture p79: CAD file, 2021-10-12]
3D PARTS/MODULES/9HP_DRUMKIT.FCStd
48.2 x 128.5 x 50.0 mm
pcb_mnt
TOP
BOTTOM
