baddy57/Eurocrack-Synth/3D PARTS/MODULES/ADSR.FCStd

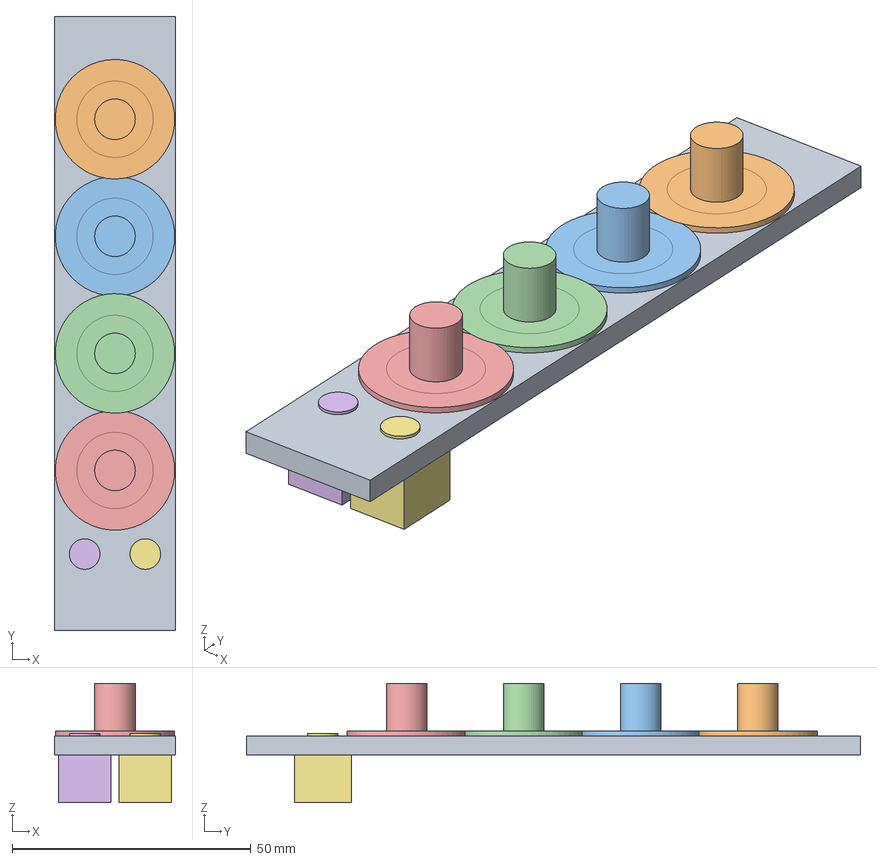
[picture p80: CAD file, 2021-10-12]
3D PARTS/MODULES/ADSR.FCStd
25.4 x 128.5 x 25.0 mm
3hp
pot
pot001
pot002
pot003
jack
jack001
