baddy57/Eurocrack-Synth/3D PARTS/MODULES/3HP_HOLDER_V3.stl

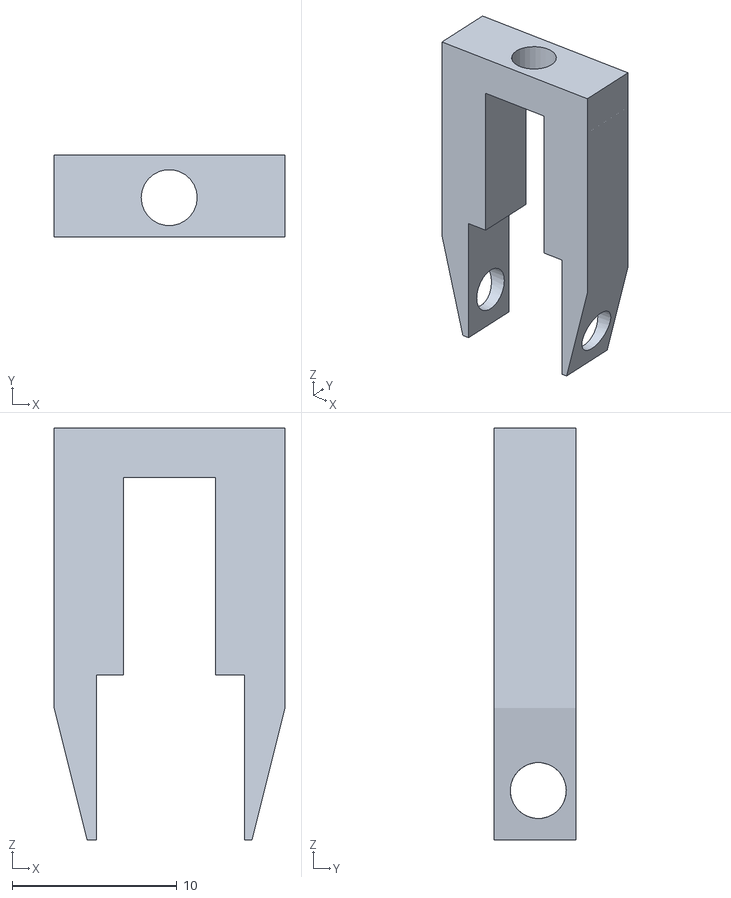
[picture p81: CAD file, 2021-10-12]
3D PARTS/MODULES/3HP_HOLDER_V3.stl
14.0 x 5.00 x 25.0
