baddy57/Eurocrack-Synth/3D PARTS/MODULES/fader knob.stl

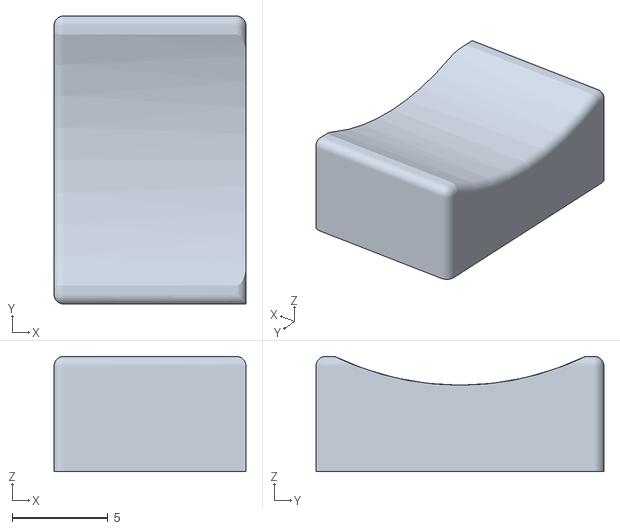
[picture p82: CAD file, 2021-10-12]
3D PARTS/MODULES/fader knob.stl
10.0 x 15.0 x 6.00
