baddy57/Eurocrack-Synth/3D PARTS/MODULES/_HOLDER_P1.stl

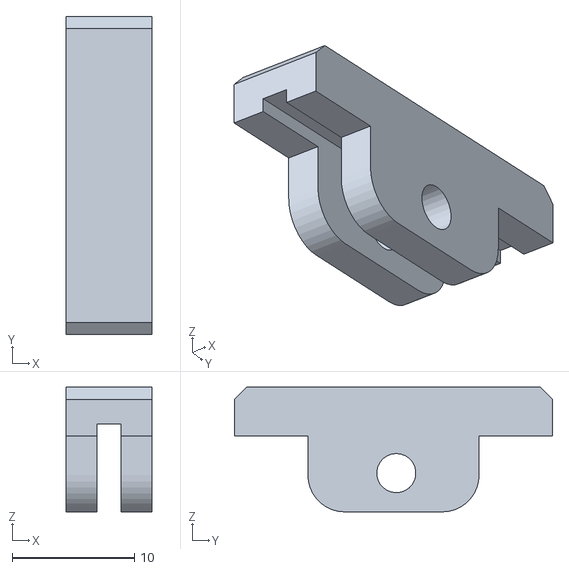
[picture p83: CAD file, 2021-10-12]
3D PARTS/MODULES/_HOLDER_P1.stl
7.00 x 26.0 x 10.2
