baddy57/Eurocrack-Synth/3D PARTS/MODULES/2HP_PCB.stl

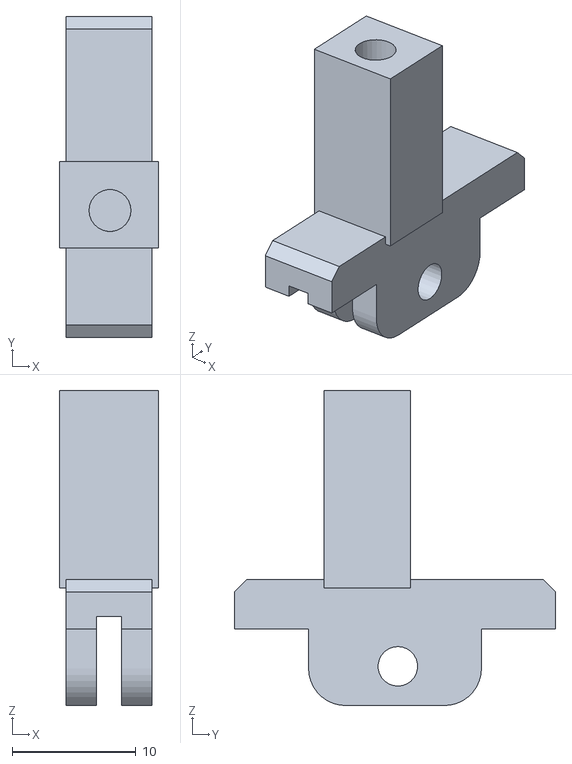
[picture p85: CAD file, 2021-10-12]
3D PARTS/MODULES/2HP_PCB.stl
8.00 x 26.0 x 25.5
