baddy57/Eurocrack-Synth/3D PARTS/MODULES/pot spacing.stl

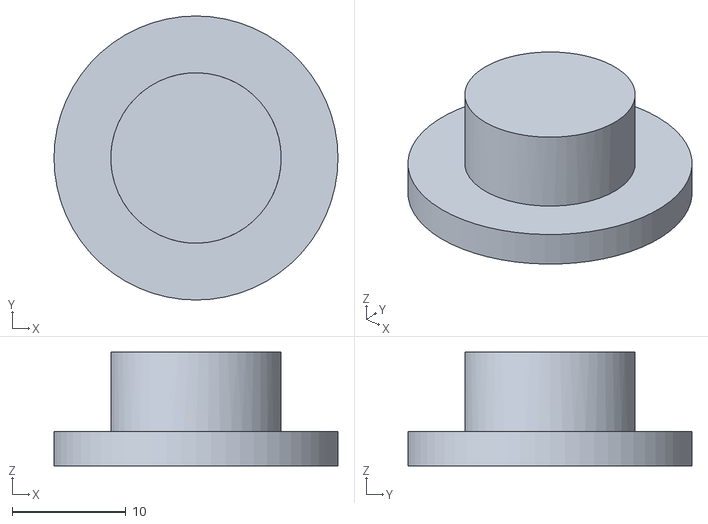
[picture p86: CAD file, 2021-10-12]
3D PARTS/MODULES/pot spacing.stl
25.0 x 25.0 x 10.0
