baddy57/Eurocrack-Synth/3D PARTS/MODULES/VCF_PCB.stl

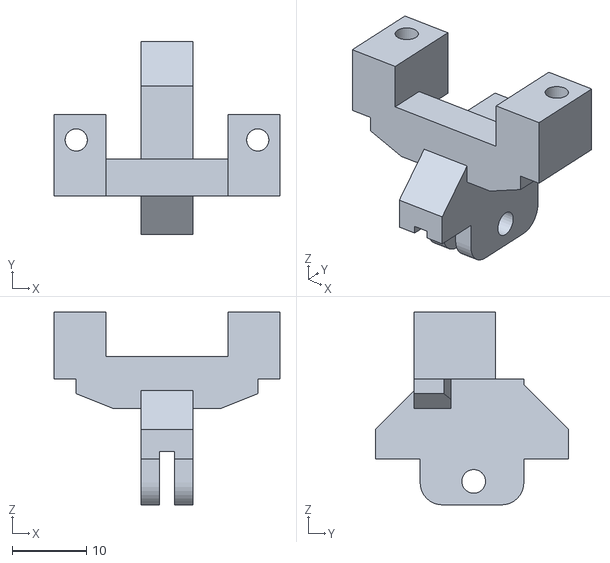
[picture p87: CAD file, 2021-10-12]
3D PARTS/MODULES/VCF_PCB.stl
30.5 x 26.0 x 26.0
