baddy57/Eurocrack-Synth/3D PARTS/MODULES/PARAMETRIC PCB HOLDER.FCStd

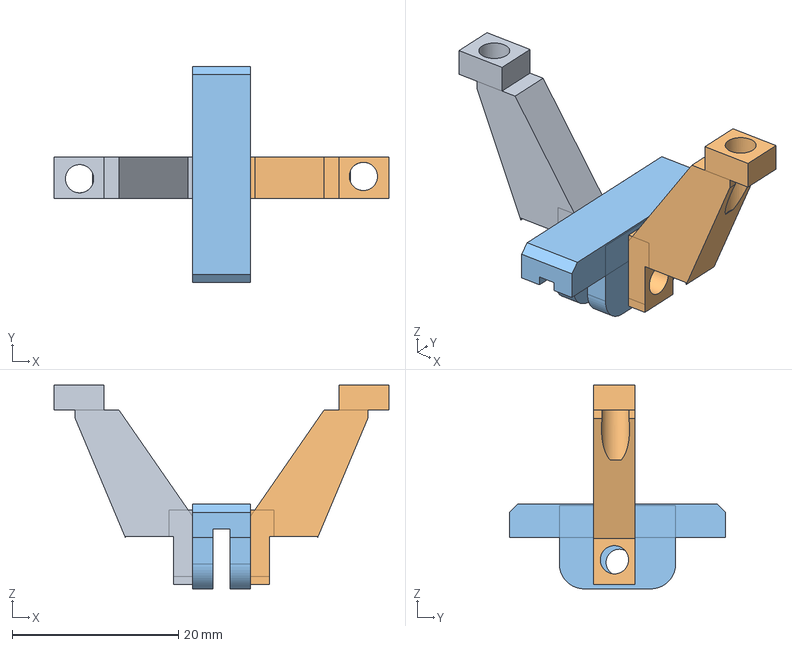
[picture p88: CAD file, 2021-10-12]
3D PARTS/MODULES/PARAMETRIC PCB HOLDER.FCStd
40.3 x 26.0 x 24.5 mm
mnt R
mnt L
pcb_mnt
