baddy57/Eurocrack-Synth/3D PARTS/MODULES/6HP_ADSR.FCStd

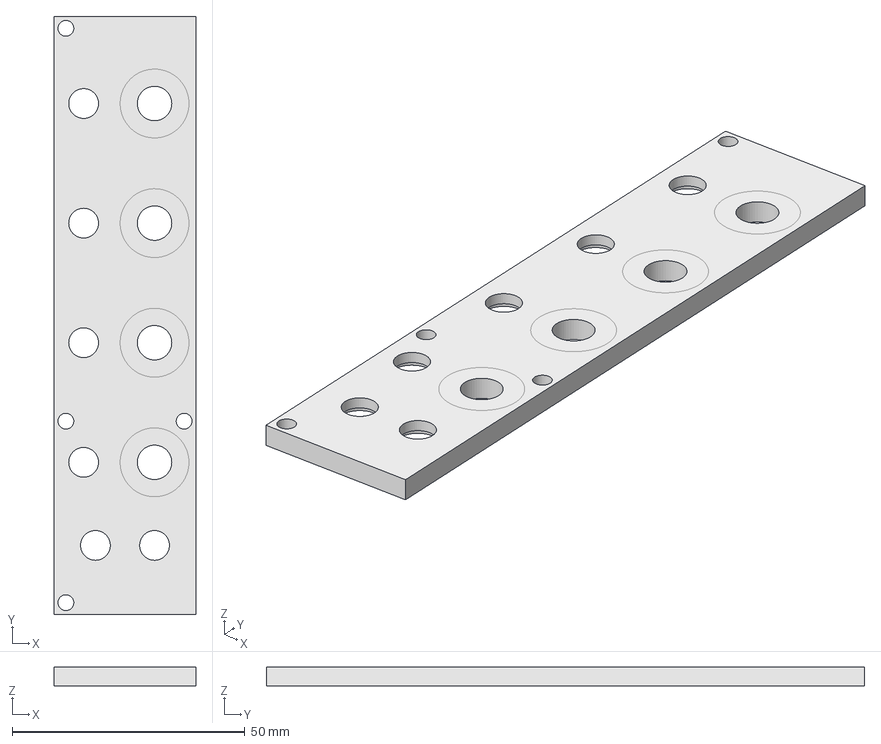
[picture p89: CAD file, 2021-10-12]
3D PARTS/MODULES/6HP_ADSR.FCStd
30.5 x 128.5 x 4.00 mm
