baddy57/Eurocrack-Synth/3D PARTS/MODULES/8HP_MIXER4_cv.FCStd

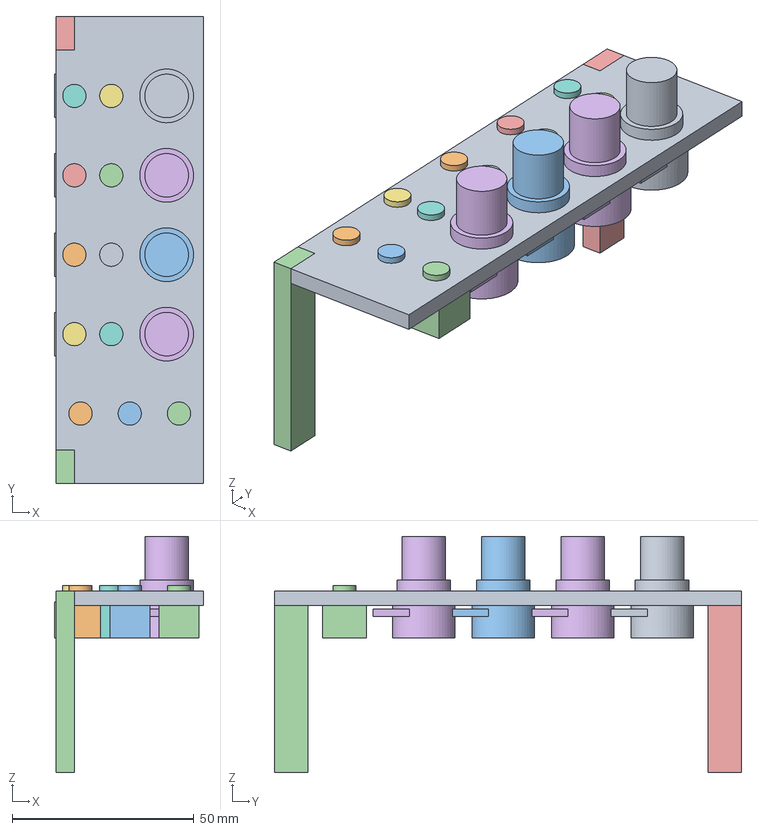
[picture p90: CAD file, 2021-10-12]
3D PARTS/MODULES/8HP_MIXER4_cv.FCStd
41.1 x 128.5 x 65.0 mm
M3 SCREW
M3 SCREW001
POTENTIOMETER
3.5 jack
3.5 jack001
3.5 jack002
3.5 jack003
POTENTIOMETER001
3.5 jack004
3.5 jack005
POTENTIOMETER002
3.5 jack006
3.5 jack007
POTENTIOMETER003
3.5 jack008
3.5 jack009
3.5 jack010
