baddy57/Eurocrack-Synth/3D PARTS/MODULES/4HP_BITCRUSHER.FCStd

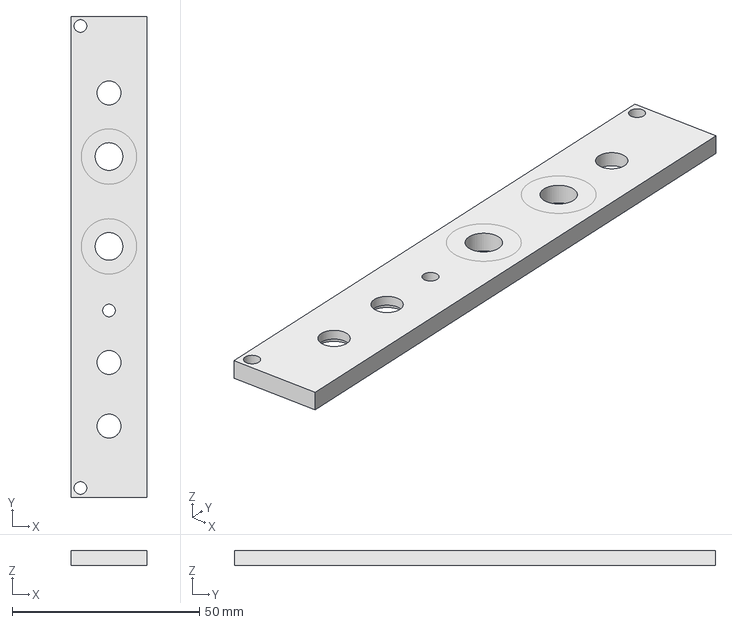
[picture p91: CAD file, 2021-10-12]
3D PARTS/MODULES/4HP_BITCRUSHER.FCStd
20.3 x 128.5 x 4.00 mm
