baddy57/Eurocrack-Synth/src/Maker.cpp

#include "Maker.h"

#include "HardwareCfg.h"
#include "Module.h"
#include "Address.h"
#include "controls/IdMux.h"

#include "modules/EmptyModule.h"
#include "modules/AudioOut.h"
#include "modules/AudioIn.h"
#include "modules/VCA.h"
#include "modules/VCO_det.h"
#include "modules/Mixer8.h"
#include "modules/MidiMono.h"
#include "modules/DrumMachine.h"
#include "modules/Vcf.h"
#include "modules/ADSR.h"

#include <cstdint>
#include <vector>

extern const uint_fast8_t MAX_MODULES;
extern ILI9341_t3 tft;

/* namespace{
	enum moduleType {
		zero, 	//0 = 0000 0000
		AUDIO_OUT,		//1 = 0000 0001
		AUDIO_IN,		//2 = 0000 0010
		MIDI_MODULE,	//3 = 0000 0011
		VCO_ID = 4,			//4 = 0000 0100
		LFO,
		FILTER,
		ADSR,
		VCA,
		MIXER8,  //9
		DISTORTION,
		REVERB,
		DELAY,
		LOOPER,
		NOISE,
		FLANGER,
		AUTOTUNE,
		DRUMS,
		INSTRUMENTS,
		EMPTY_MODULE = 255
	};
}; */

//array of pointers to foos(constructors)?
	//case VCO return new constructors[VCO]
//no switch case?
	//return new constructors[moduleType]
//uint_fast8_t connected_modules =0;

void
Maker :: createModules (std::vector<Module*>& vm) {	
	bool verbose = true;
	for (uint_fast8_t i = 0; i < MAX_MODULES; ++i) {
		Address slotAddress(i);
		uint_fast8_t moduleType = IdMux(slotAddress).getModuleId();
		switch (moduleType) {
		case 0: {
			break;
		}

		case 1: {
			if (verbose) {
				tft.print(moduleType);
				tft.print("  AUDIO_OUT");
				tft.print("  @  ");
				tft.println(slotAddress.toInt());
			}
			vm.push_back(new AudioOut(slotAddress));
			break;
		}
		case 2: {
			if (verbose) {
				tft.print(moduleType);
				tft.print("  AUDIO_IN");
				tft.print("  @  ");
				tft.println(slotAddress.toInt());
			}
			vm.push_back(new AudioIn(slotAddress));
			break;
		}
		case 3: {
			if (verbose) {
				tft.print(moduleType);
				tft.print("  VCF");
				tft.print("  @  ");
				tft.println(slotAddress.toInt());
			}
			vm.push_back(new VCF(slotAddress));
			break;
		}
		case 4: {
			if (verbose) {
				tft.print(moduleType);
				tft.print("  VCO_det");
				tft.print("  @  ");
				tft.println(slotAddress.toInt());
			}
			//++connected_modules;
			vm.push_back(new VCO_det(slotAddress));
			break;
		}
		case 5: {
			if (verbose) {
				tft.print(moduleType);
				tft.print("  MIDI MONO");
				tft.print("  @  ");
				tft.println(slotAddress.toInt());
			}
			//++connected_modules;
			vm.push_back(new MidiMono(slotAddress));
			break;
		}
		case 6: {
			if (verbose) {
				tft.print(moduleType);
				tft.print("  ADSR");
				tft.print("  @  ");
				tft.println(slotAddress.toInt());
			}
			//++connected_modules;
			vm.push_back(new ADSR(slotAddress));
			break;
		}
		case 9: {
			if (verbose) {
				tft.print(moduleType);
				tft.print("  MIXER8");
				tft.print("  @  ");
				tft.println(slotAddress.toInt());
			}
			//++connected_modules;
			vm.push_back(new Mixer8(slotAddress));
			break;
		}
		case 10: {
			if (verbose) {
				tft.print(moduleType);
				tft.print("  VCA");
				tft.print("  @  ");
				tft.println(slotAddress.toInt());
			}
			//++connected_modules;
			vm.push_back(new VCA(slotAddress));
			break;
		}
		case 11: {
			if (verbose) {
				tft.print(moduleType);
				tft.print("  DRUMZ");
				tft.print("  @  ");
				tft.println(slotAddress.toInt());
			}
			//++connected_modules;
			vm.push_back(new DrumMachine(slotAddress));
			break;
		}
		default: {
			break;
		}
		};

	}
}
